jon-le0234/DoomScroller/Images/DoomScroller/01.png

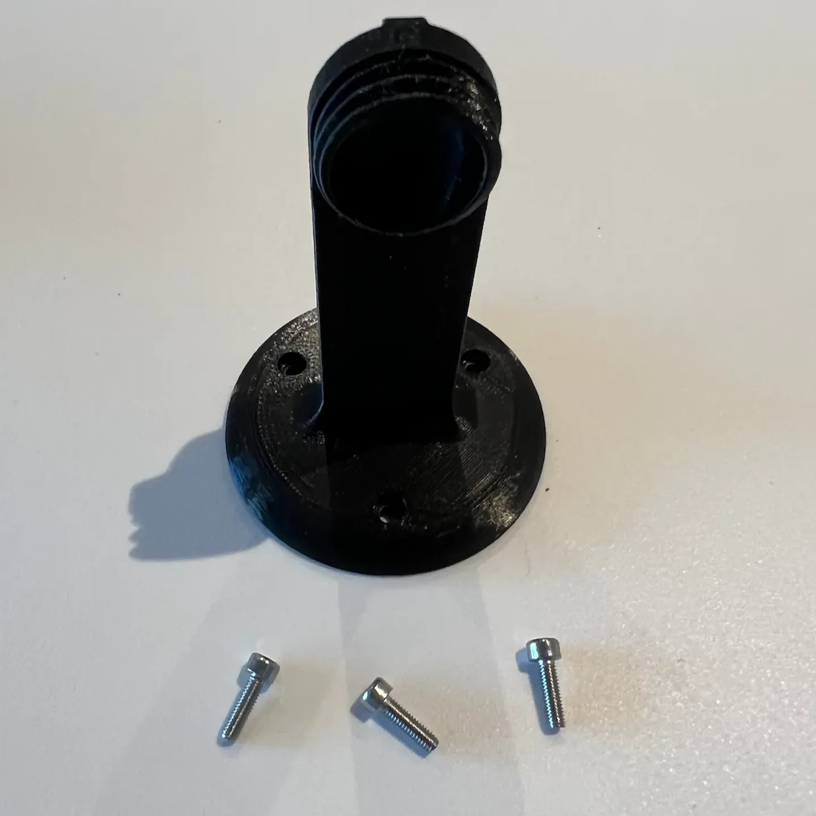
Images/DoomScroller/01.png
