jon-le0234/DoomScroller/Images/DoomScroller/02.png

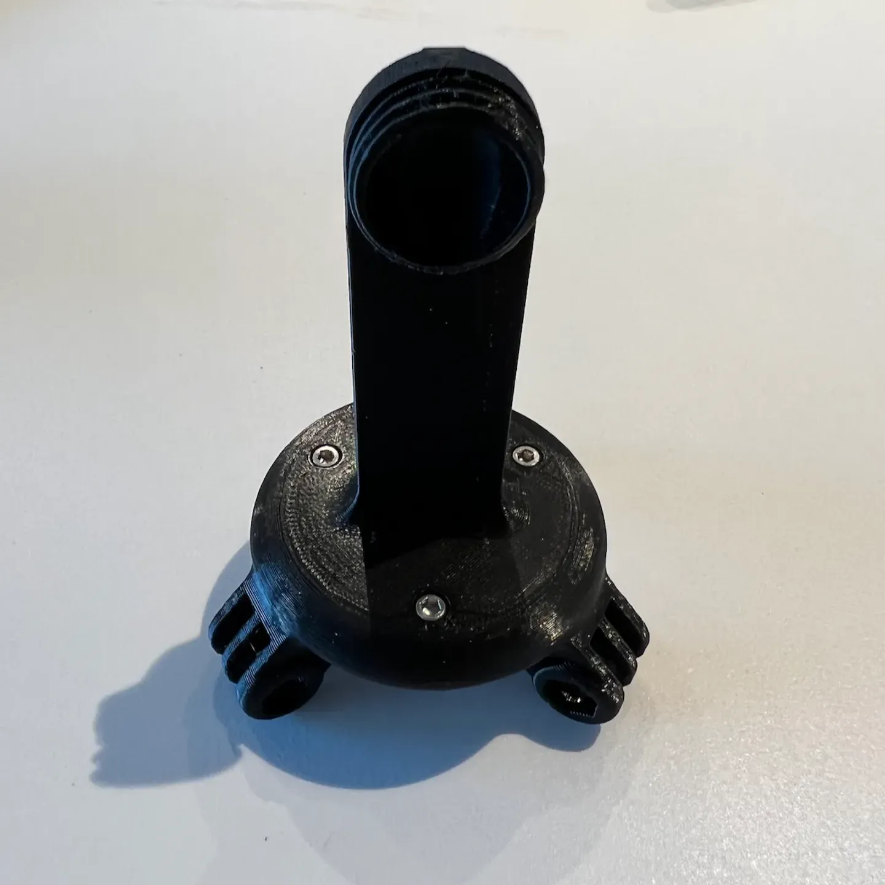
Images/DoomScroller/02.png
