jon-le0234/DoomScroller/Images/DoomScroller/03.png

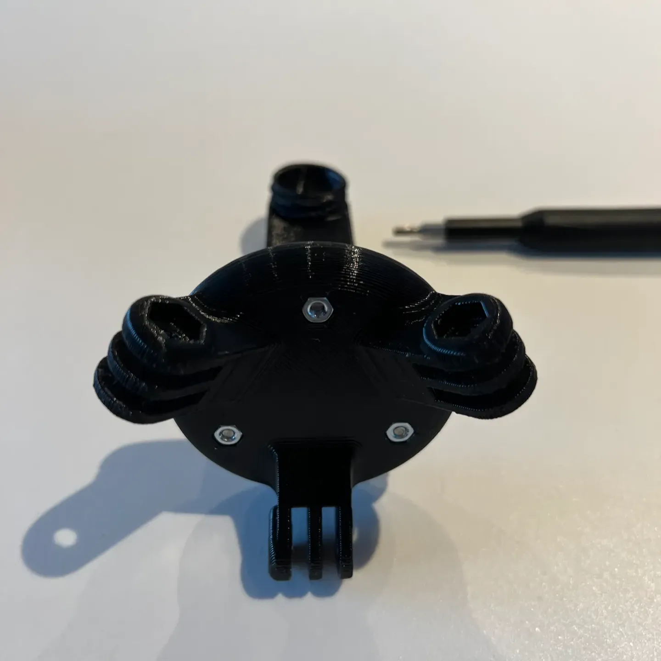
Images/DoomScroller/03.png
