jon-le0234/DoomScroller/Images/DoomScroller/04.png

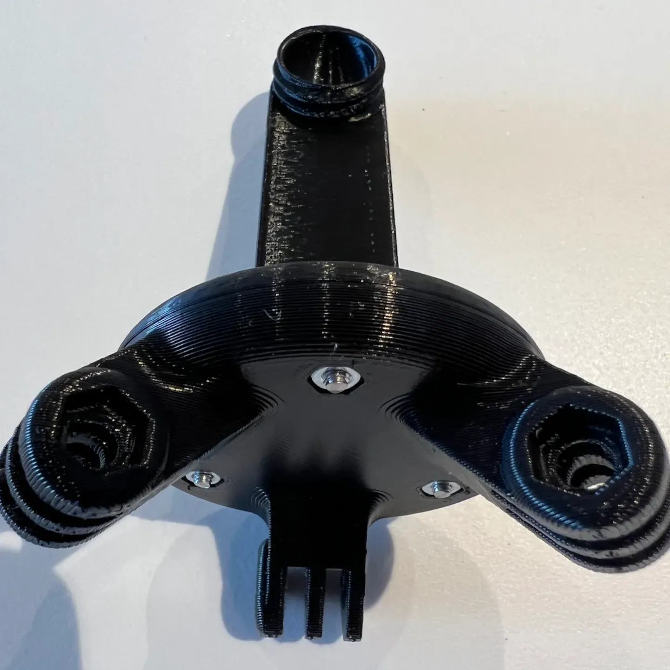
Images/DoomScroller/04.png
