jon-le0234/DoomScroller/Images/DoomScroller/05.png

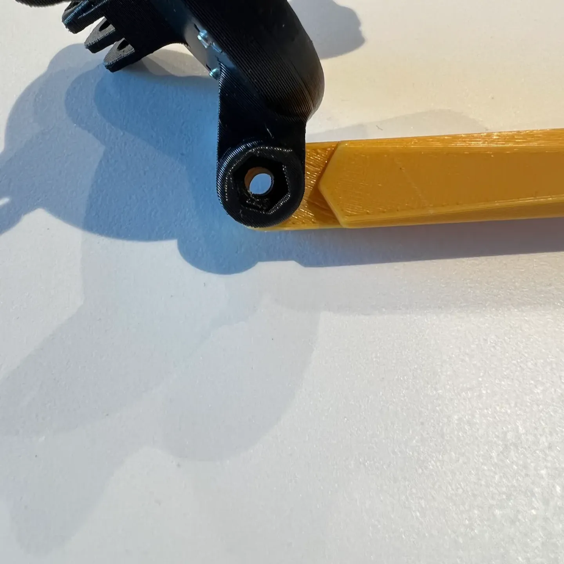
Images/DoomScroller/05.png
