jon-le0234/DoomScroller/Images/DoomScroller/06.png

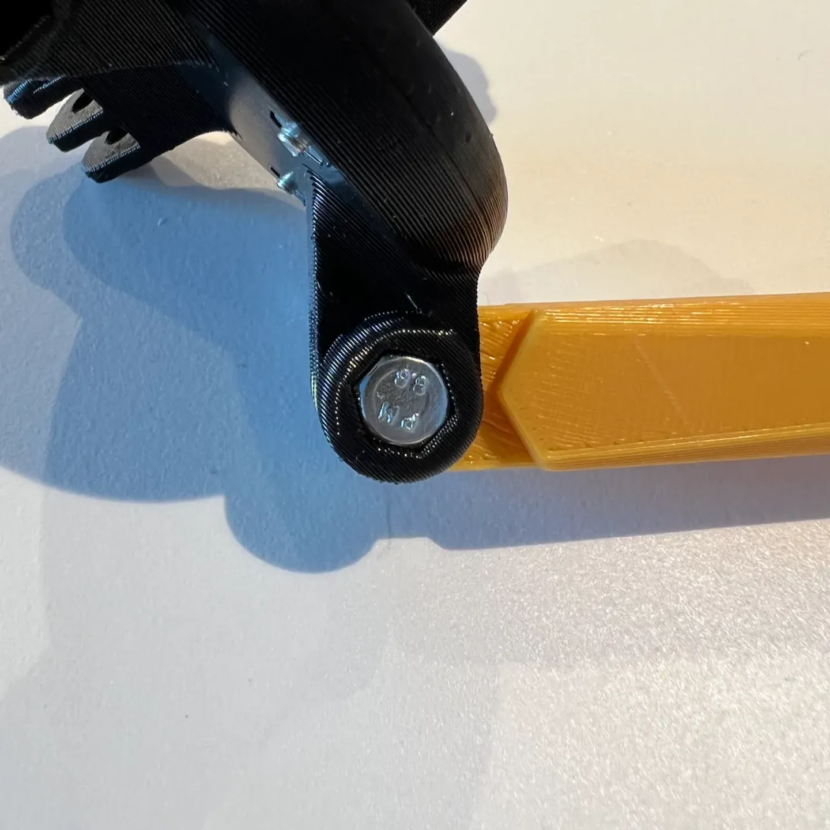
Images/DoomScroller/06.png
