jon-le0234/DoomScroller/Images/DoomScroller/07.png

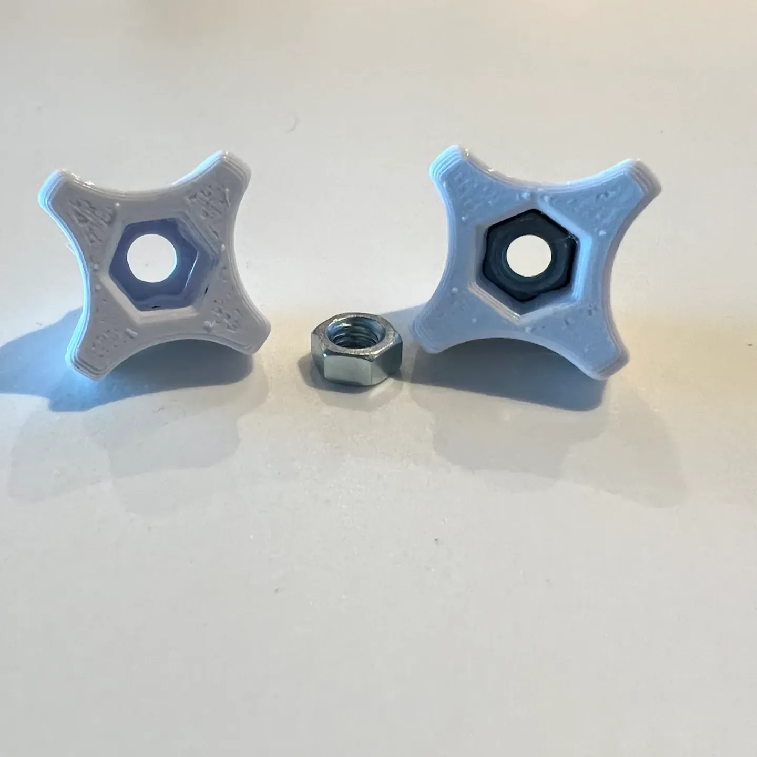
Images/DoomScroller/07.png
