jon-le0234/DoomScroller/Images/DoomScroller/08.png

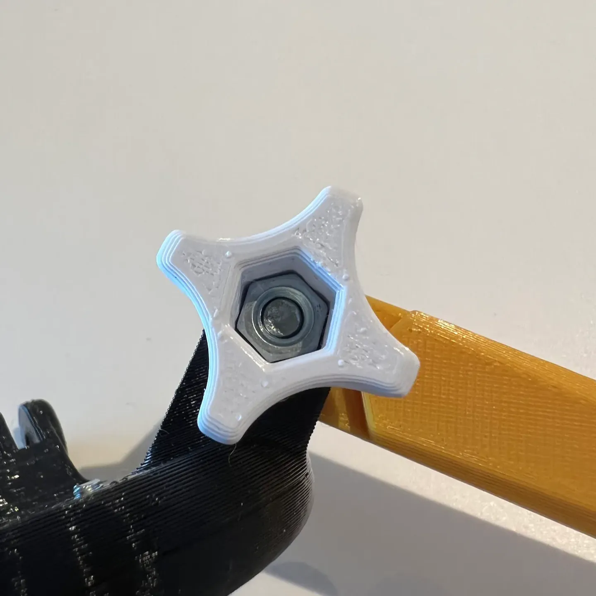
Images/DoomScroller/08.png
