jon-le0234/DoomScroller/Images/DoomScroller/09.png

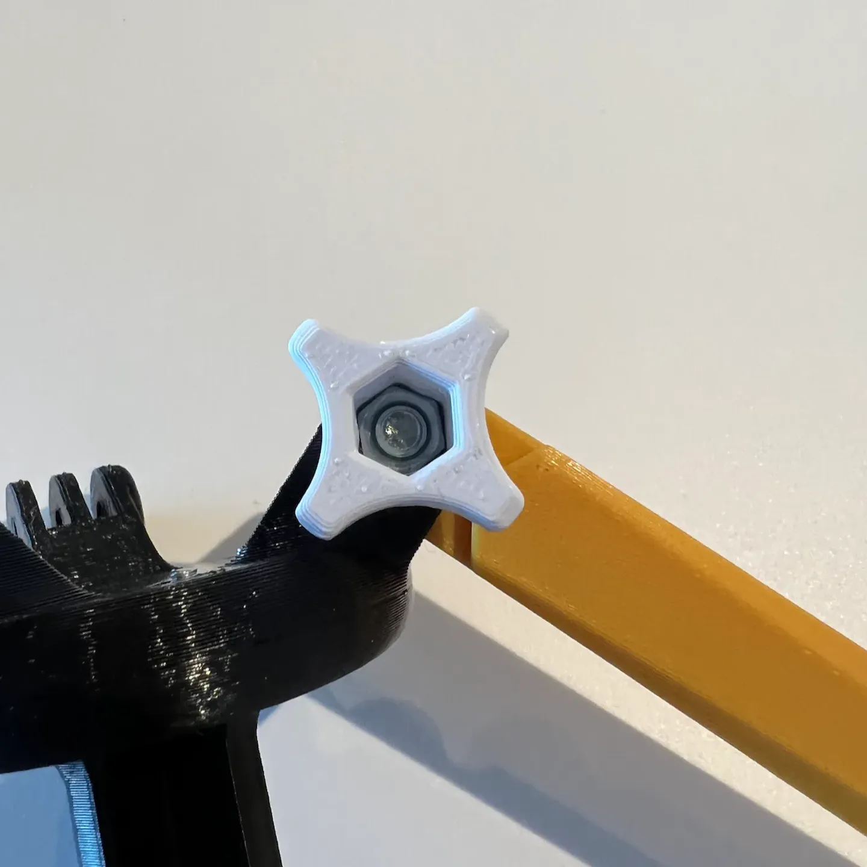
Images/DoomScroller/09.png
