jon-le0234/DoomScroller/Images/DoomScroller/10.png

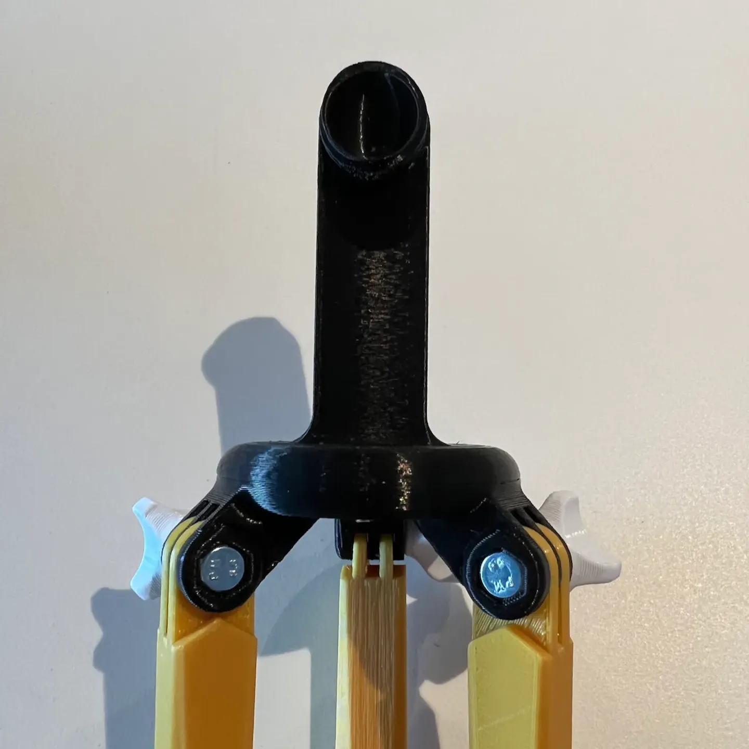
Images/DoomScroller/10.png
