jon-le0234/DoomScroller/Images/DoomScroller/11.png

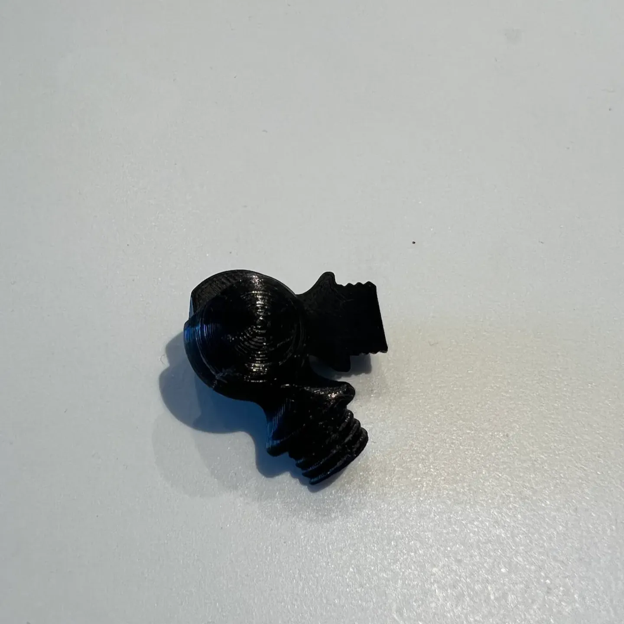
Images/DoomScroller/11.png
