jon-le0234/DoomScroller/Images/DoomScroller/12.png

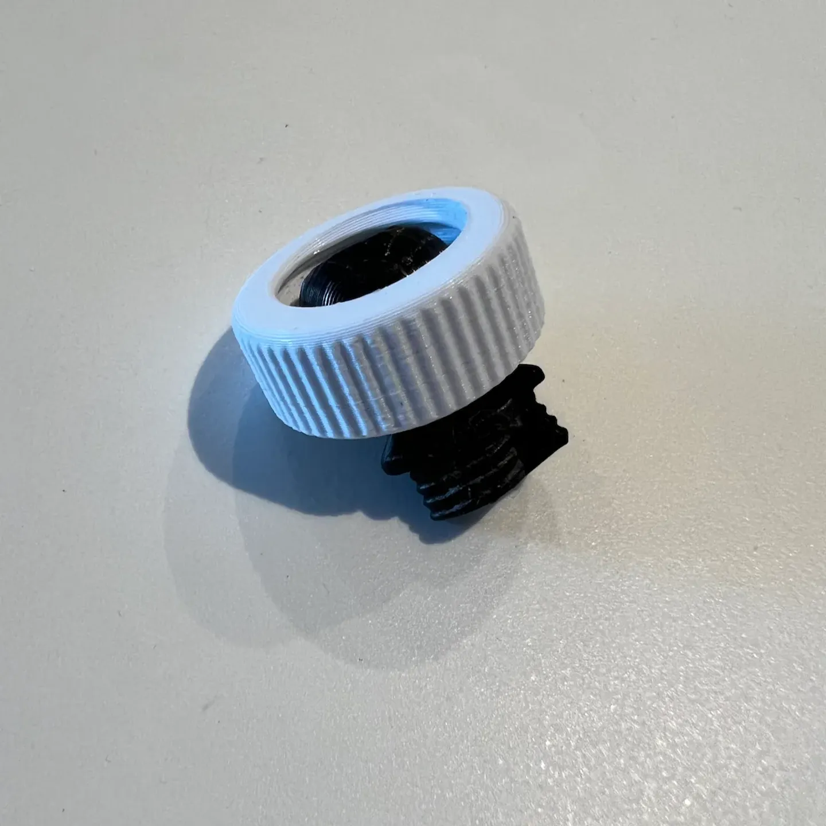
Images/DoomScroller/12.png
