jon-le0234/DoomScroller/Images/DoomScroller/13.png

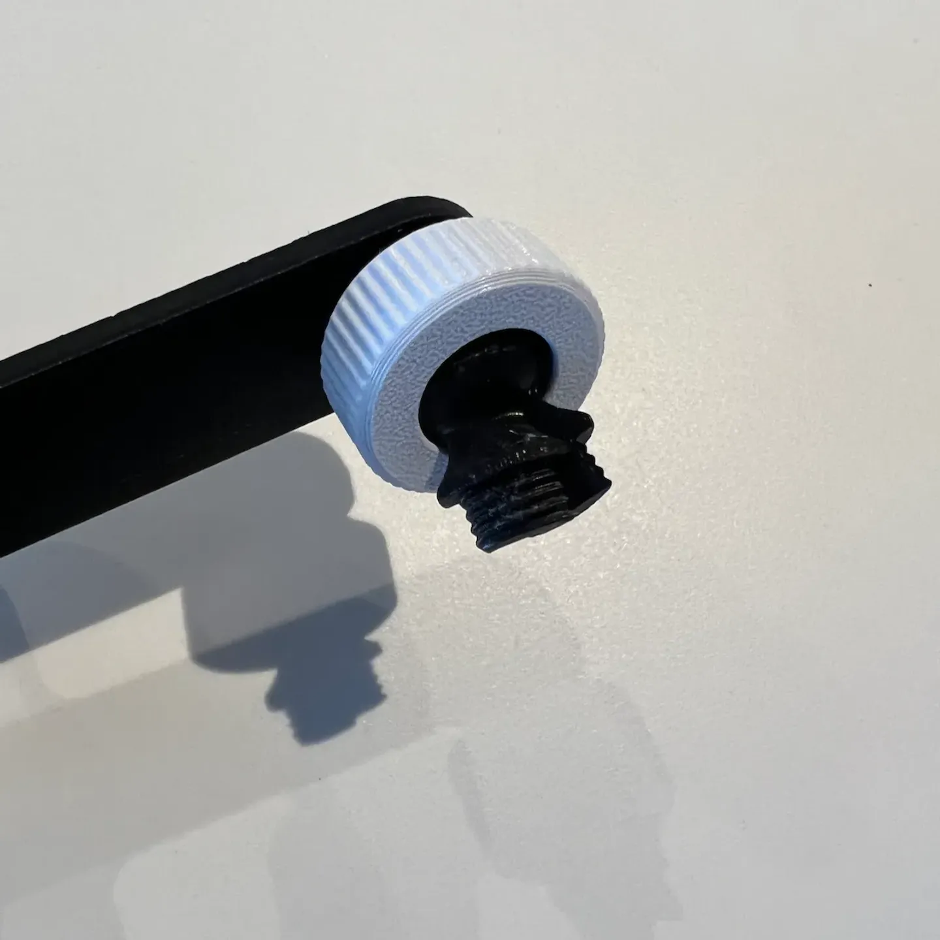
Images/DoomScroller/13.png
