jon-le0234/DoomScroller/Images/DoomScroller/14.png

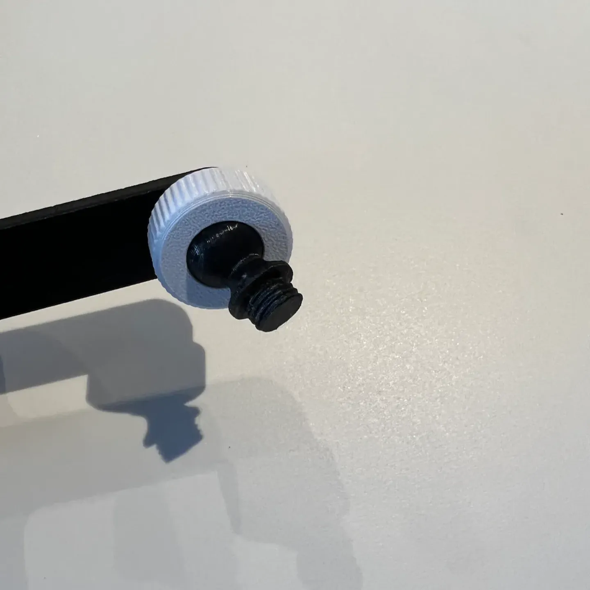
Images/DoomScroller/14.png
