jon-le0234/DoomScroller/Images/DoomScroller/15a.png

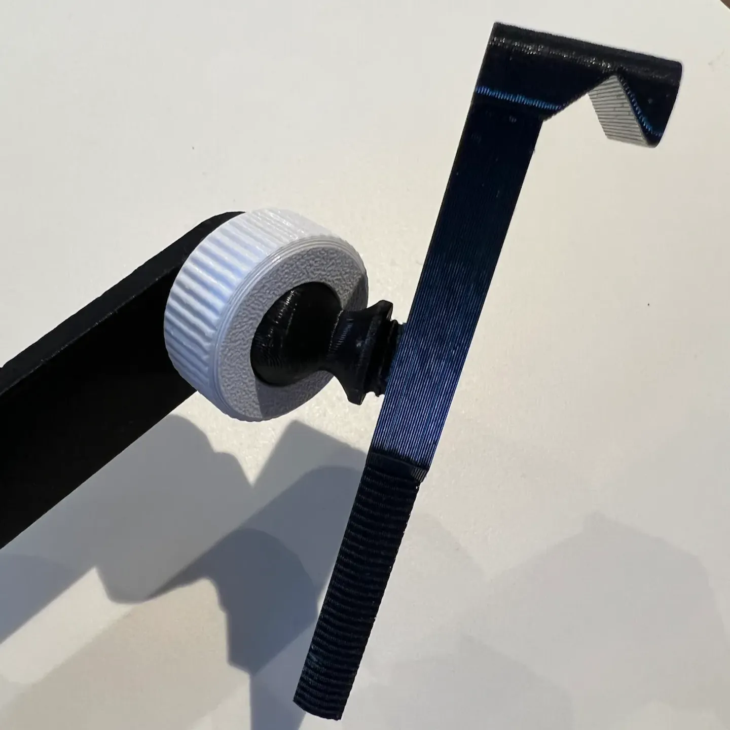
Images/DoomScroller/15a.png
