jon-le0234/DoomScroller/Images/DoomScroller/16.png

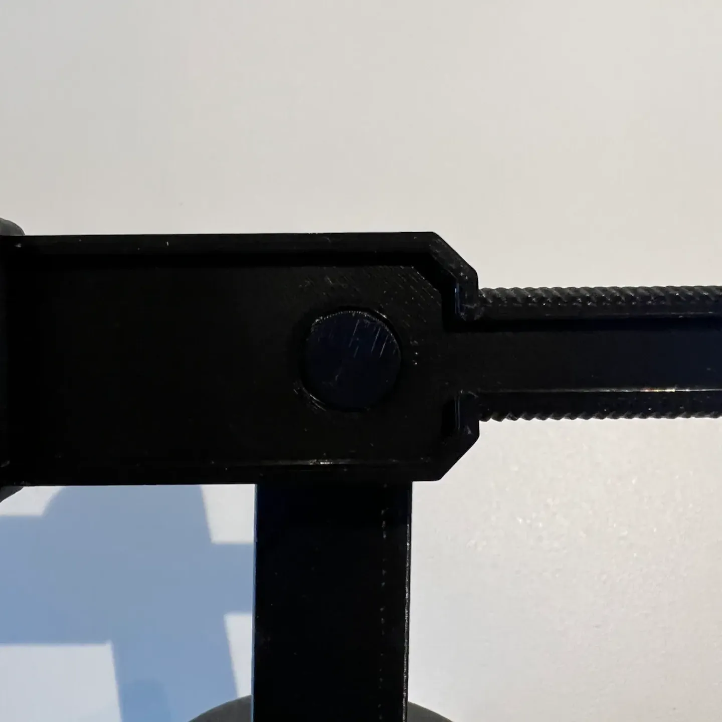
Images/DoomScroller/16.png
