jon-le0234/DoomScroller/Images/DoomScroller/17.png

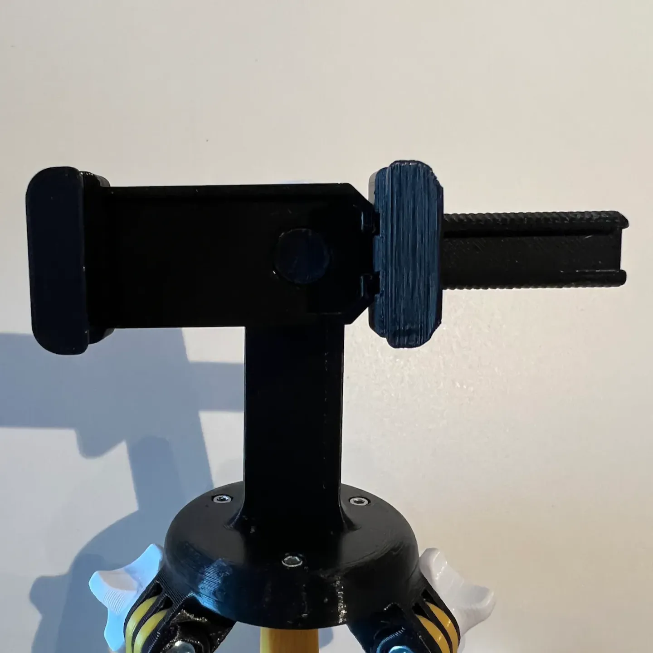
Images/DoomScroller/17.png
