jon-le0234/DoomScroller/Images/DoomScroller/18.png

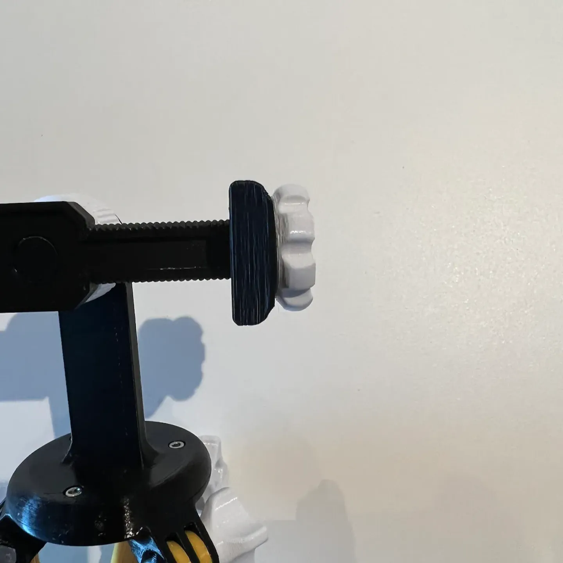
Images/DoomScroller/18.png
