jon-le0234/DoomScroller/Images/DoomScroller/black-blue-purple.png

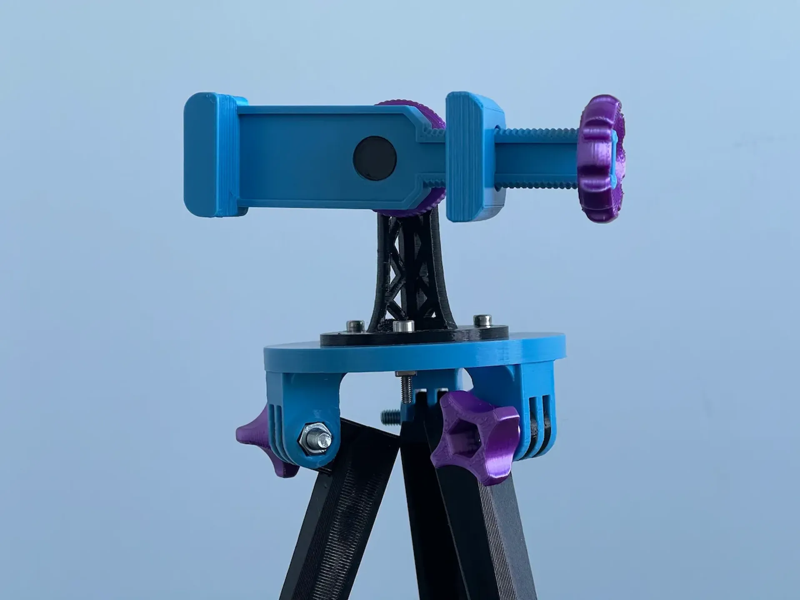
Images/DoomScroller/black-blue-purple.png
