jon-le0234/DoomScroller/Images/DoomScroller/black-blue.png

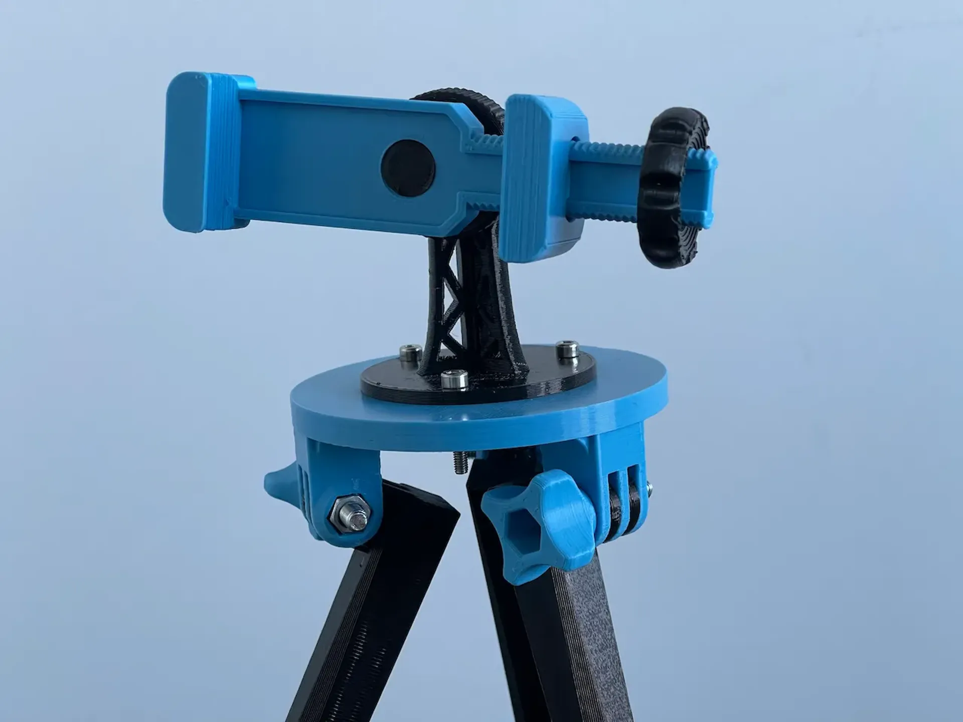
Images/DoomScroller/black-blue.png
