jon-le0234/DoomScroller/Images/DoomScroller/black-gold.png

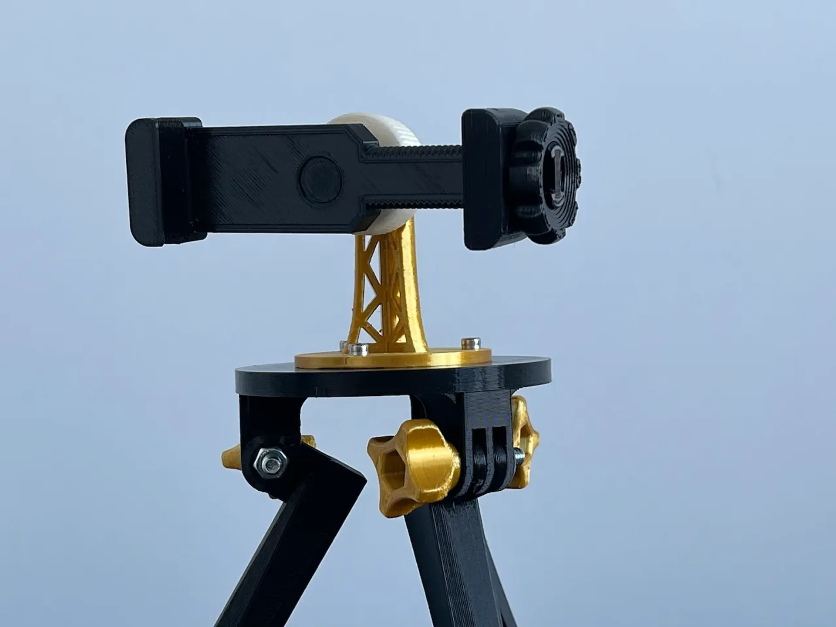
Images/DoomScroller/black-gold.png
