jon-le0234/DoomScroller/Images/DoomScroller/black-green.png

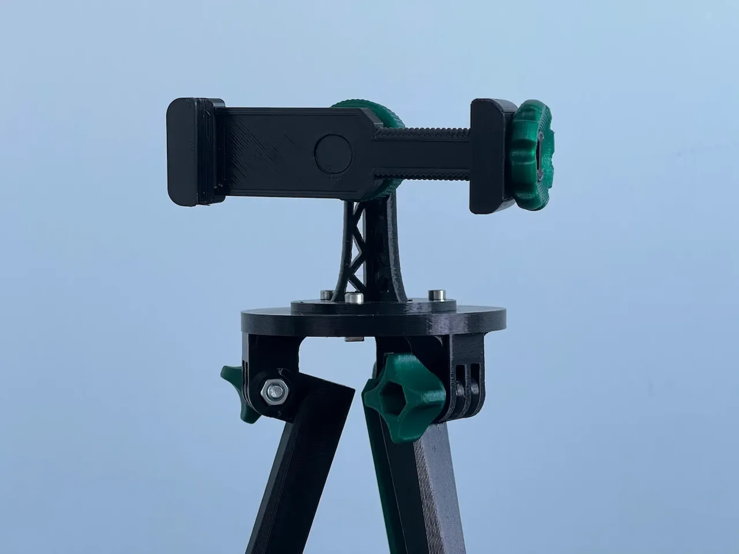
Images/DoomScroller/black-green.png
