jon-le0234/DoomScroller/Images/DoomScroller/black-purple.png

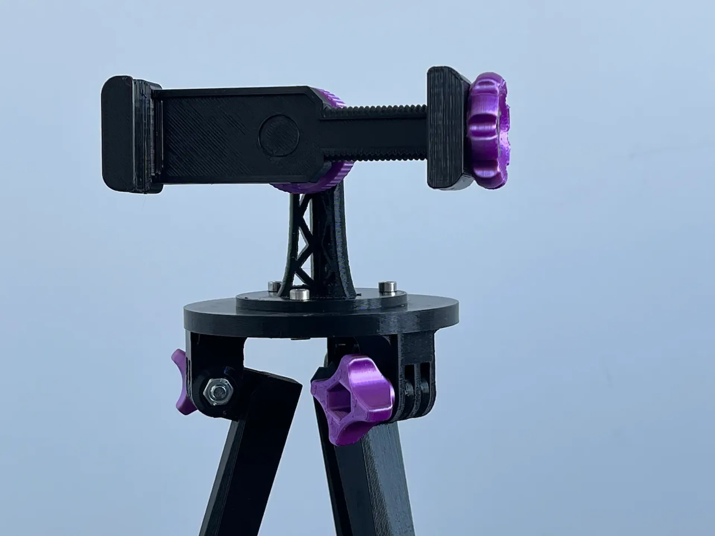
Images/DoomScroller/black-purple.png
