jon-le0234/DoomScroller/Images/DoomScroller/black-red-green.png

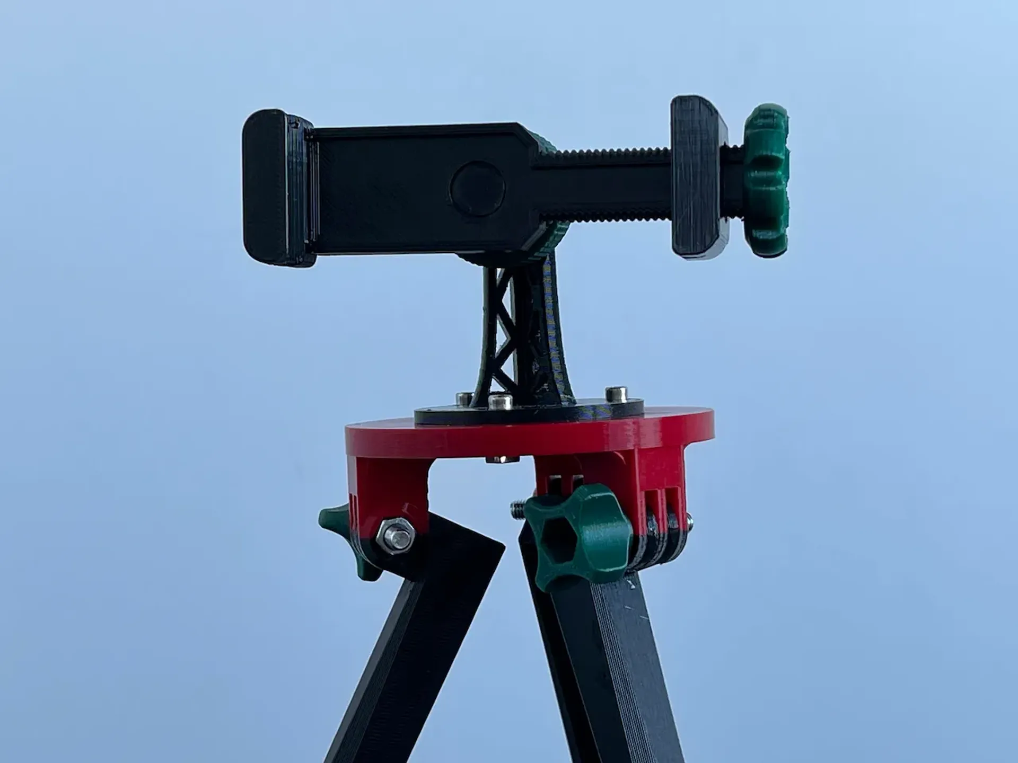
Images/DoomScroller/black-red-green.png
