jon-le0234/DoomScroller/Images/DoomScroller/black-red.png

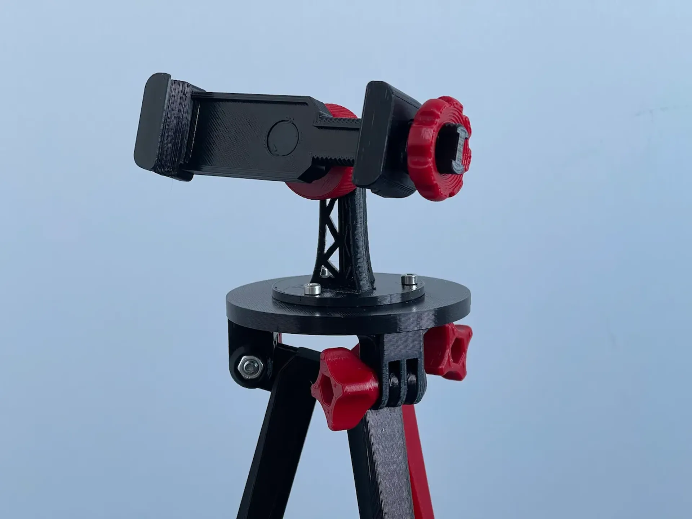
Images/DoomScroller/black-red.png
