jon-le0234/DoomScroller/Images/DoomScroller/doomscroller-panavise.png

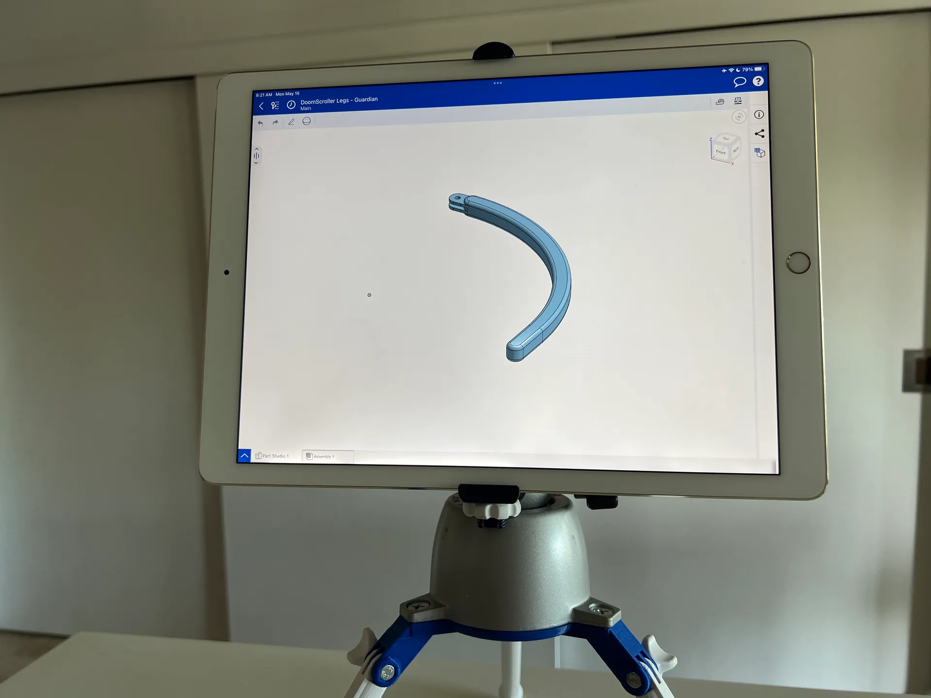
Images/DoomScroller/doomscroller-panavise.png
