jon-le0234/DoomScroller/Images/DoomScroller/gold-black.png

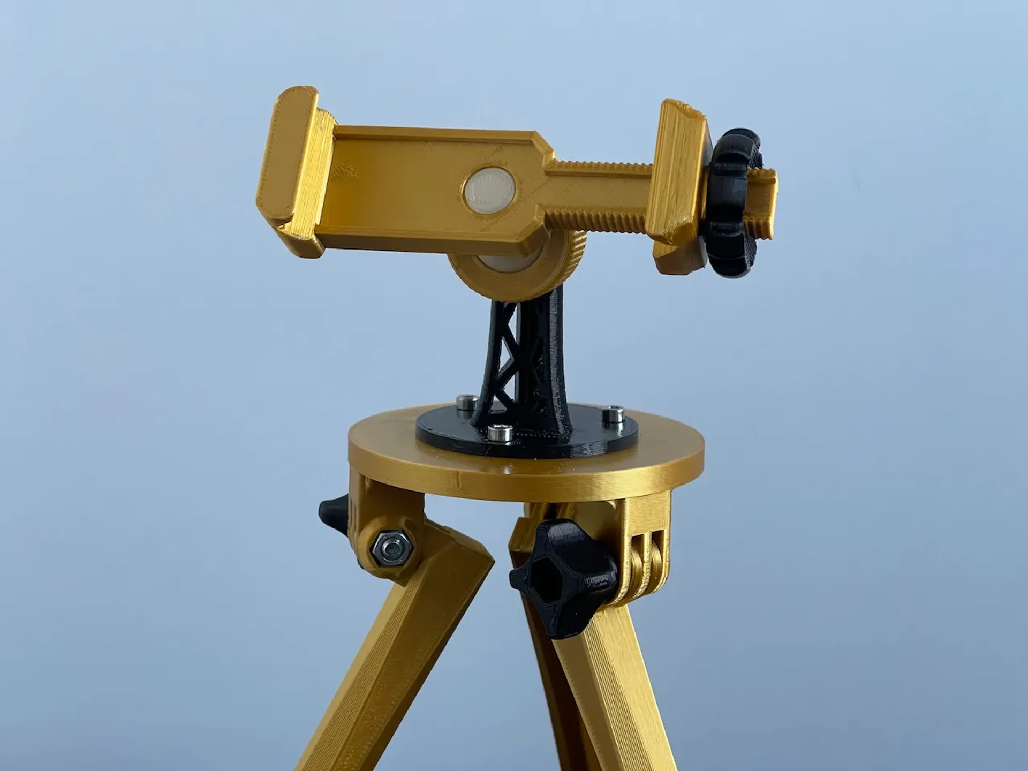
Images/DoomScroller/gold-black.png
