jon-le0234/DoomScroller/Images/DoomScroller/jon-and-jo.png

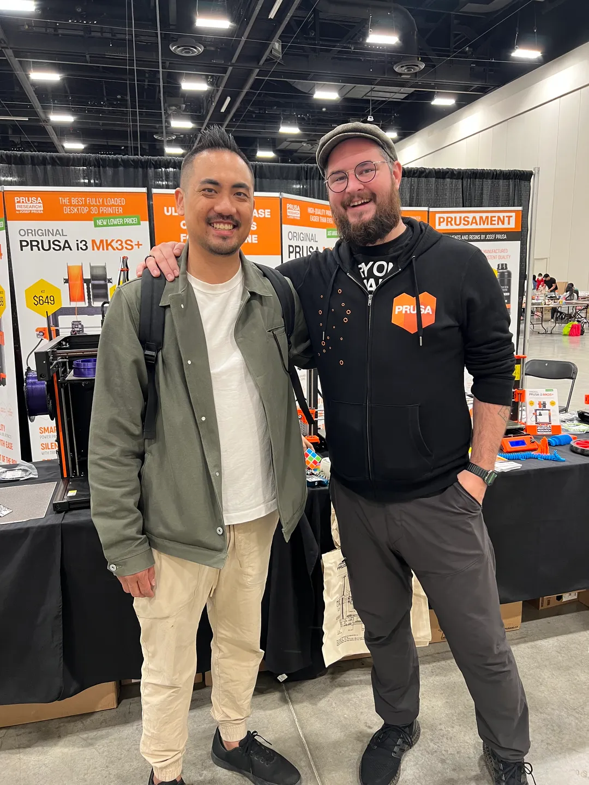
Images/DoomScroller/jon-and-jo.png
