jon-le0234/DoomScroller/Images/DoomScroller/lakers.png

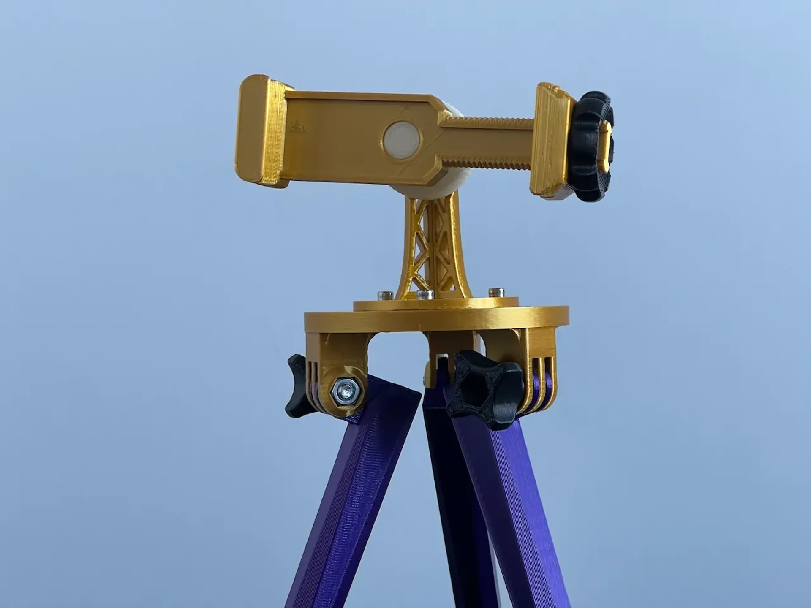
Images/DoomScroller/lakers.png
