jon-le0234/DoomScroller/Images/DoomScroller/landscape.png

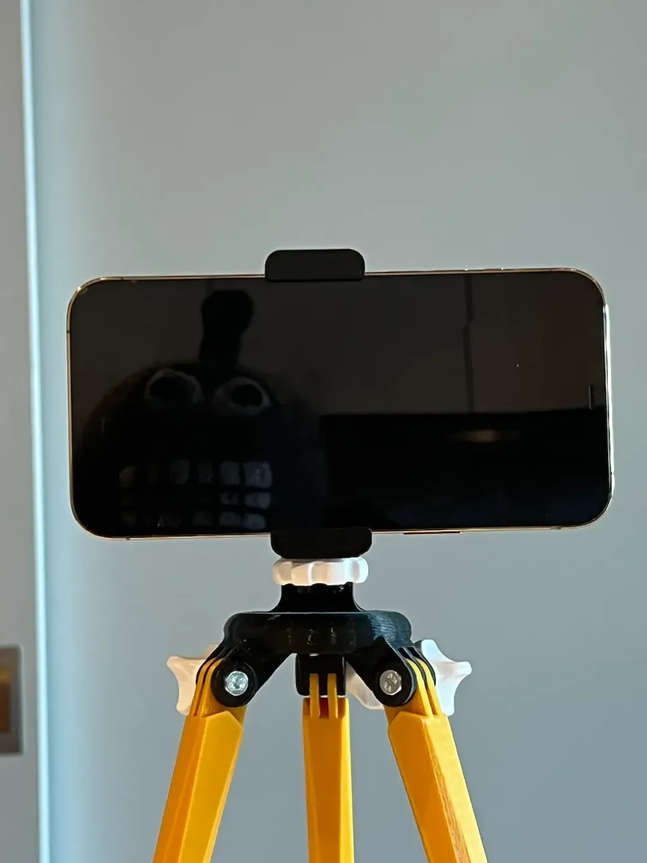
Images/DoomScroller/landscape.png
