jon-le0234/DoomScroller/Images/DoomScroller/oilers.png

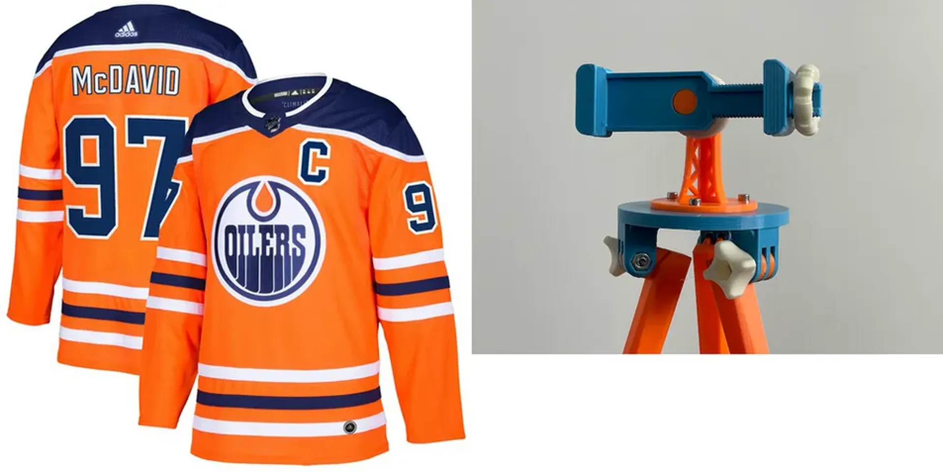
Images/DoomScroller/oilers.png
