jon-le0234/DoomScroller/Images/DoomScroller/red-purple.png

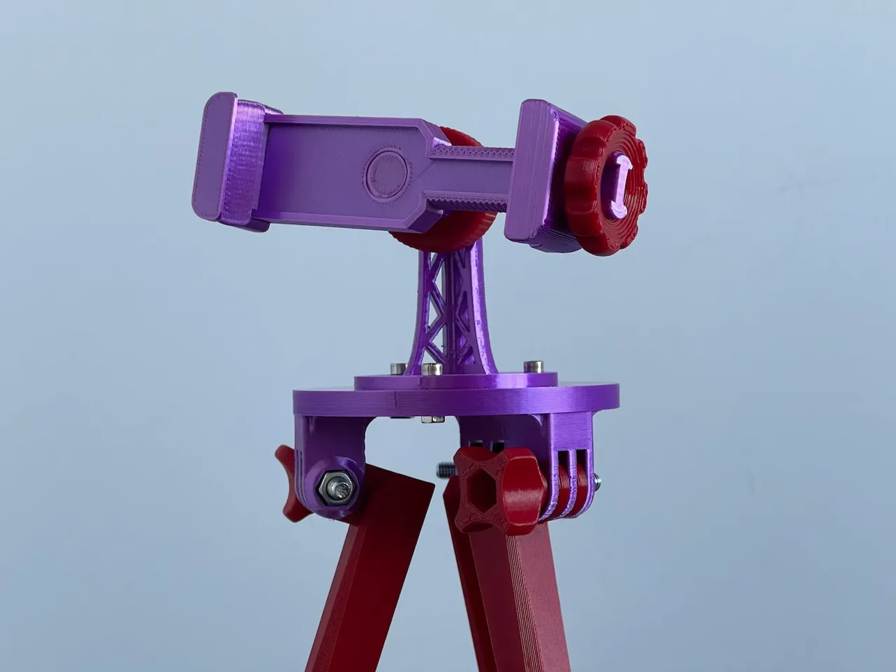
Images/DoomScroller/red-purple.png
