jon-le0234/DoomScroller/Images/Mini DoomScroller/01.png

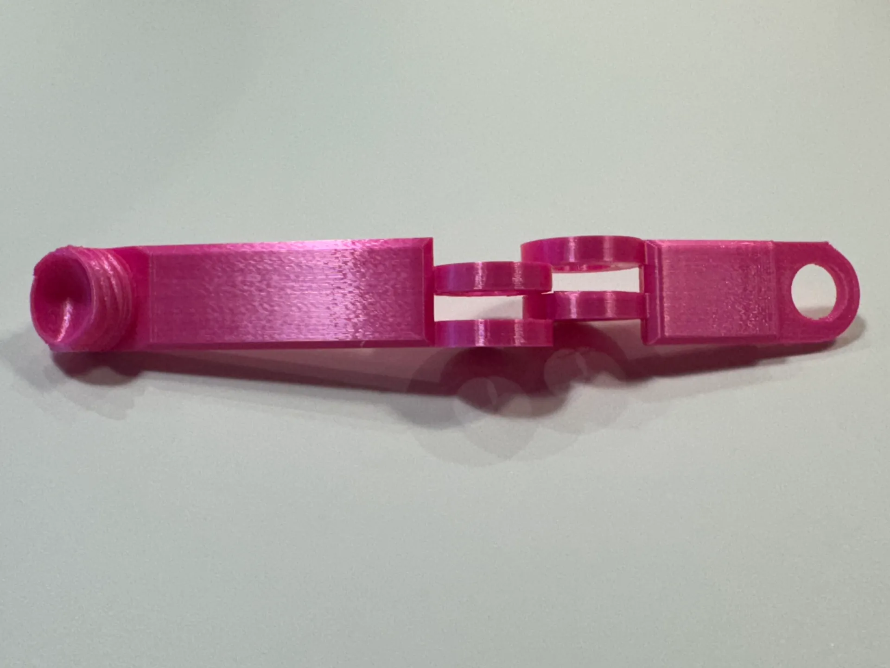
Images/Mini DoomScroller/01.png
