jon-le0234/DoomScroller/Images/Mini DoomScroller/02.png

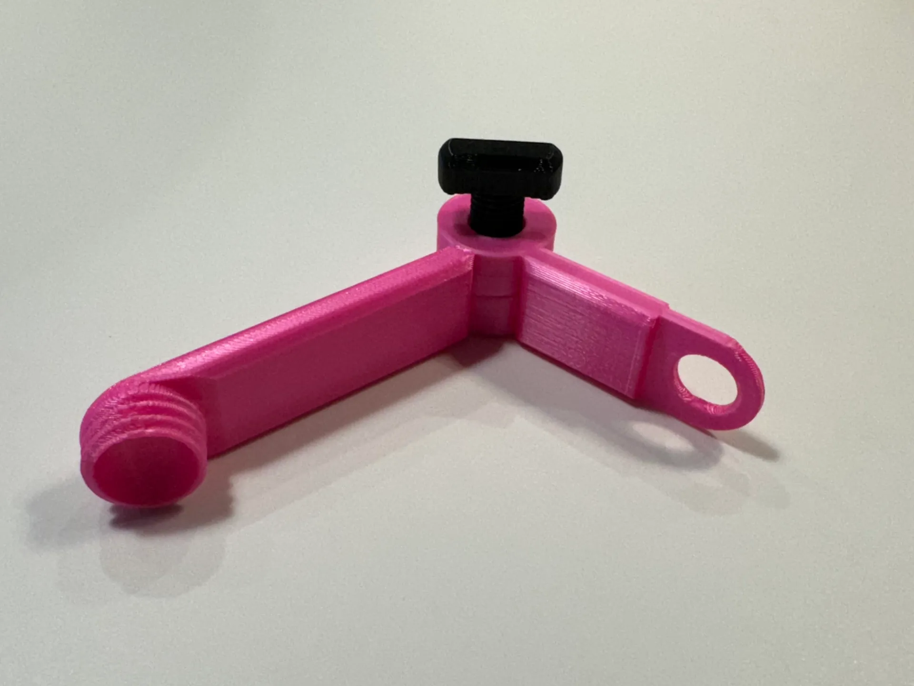
Images/Mini DoomScroller/02.png
