jon-le0234/DoomScroller/Images/Mini DoomScroller/03.png

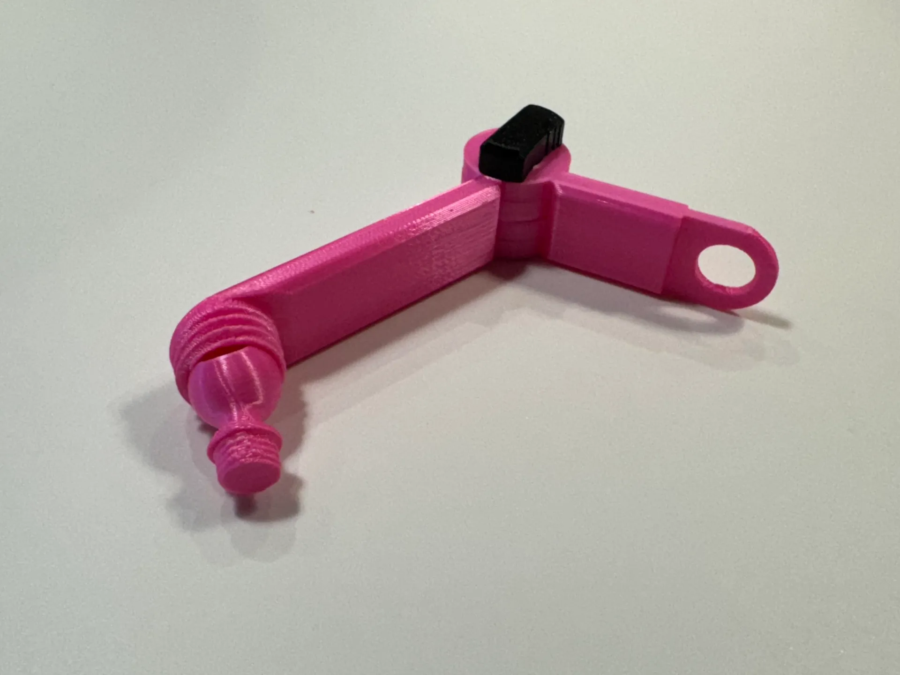
Images/Mini DoomScroller/03.png
