jon-le0234/DoomScroller/Images/Mini DoomScroller/04.png

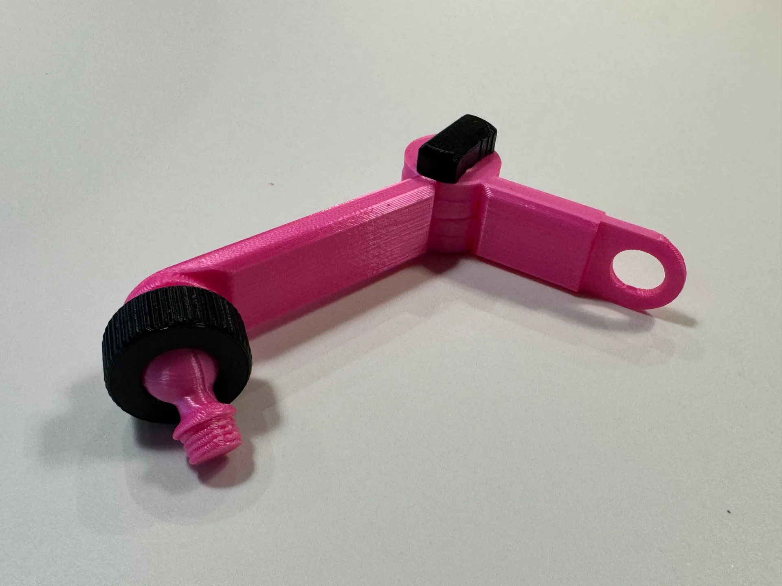
Images/Mini DoomScroller/04.png
