jon-le0234/DoomScroller/Images/Mini DoomScroller/05.png

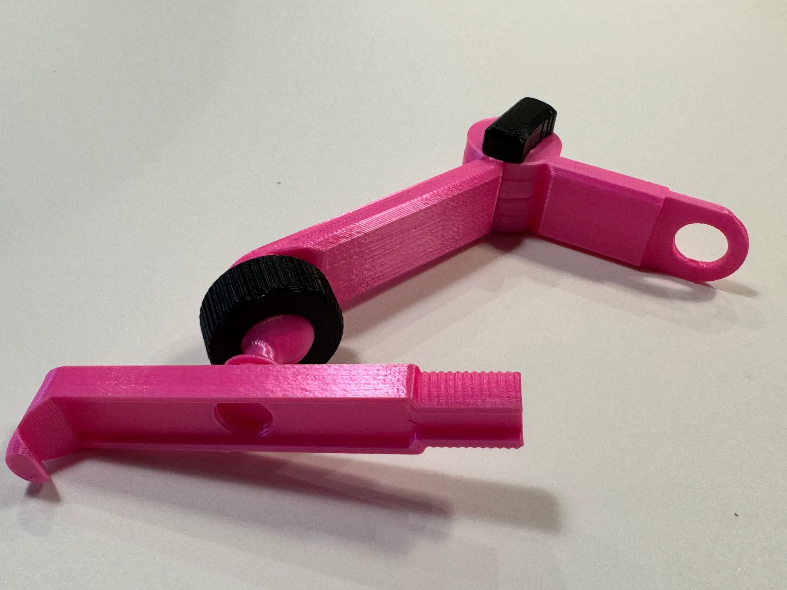
Images/Mini DoomScroller/05.png
