jon-le0234/DoomScroller/Images/Mini DoomScroller/06.png

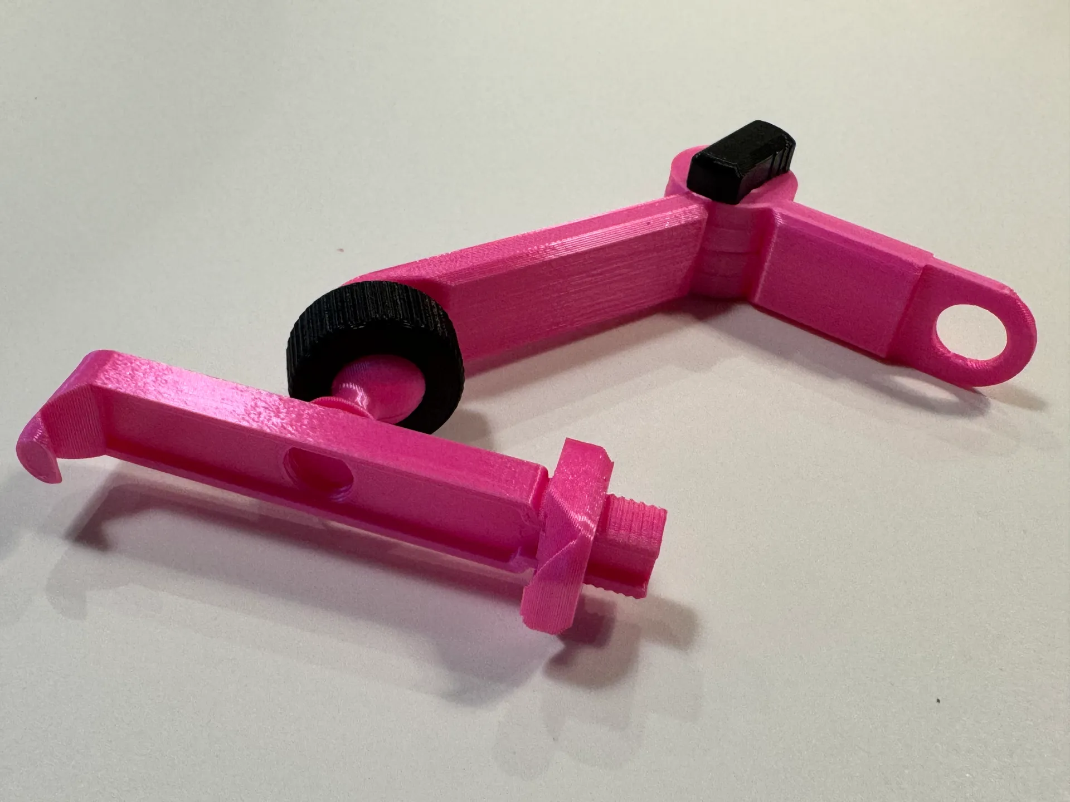
Images/Mini DoomScroller/06.png
