jon-le0234/DoomScroller/Images/Mini DoomScroller/07.png

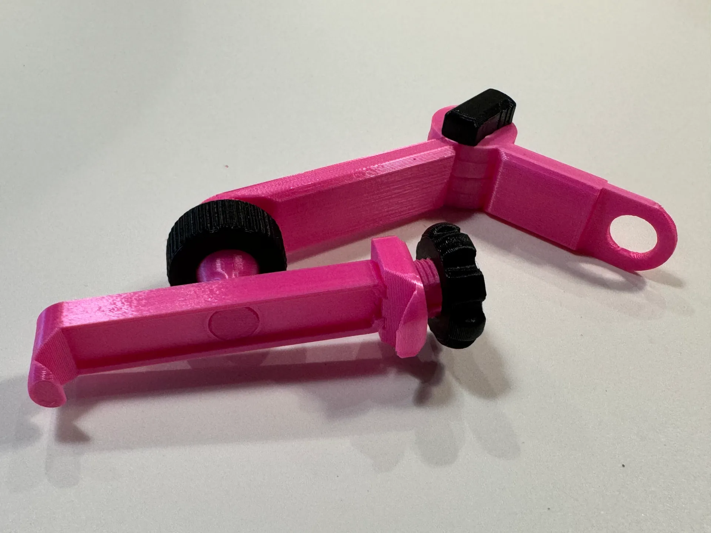
Images/Mini DoomScroller/07.png
