jon-le0234/DoomScroller/Images/Mini DoomScroller/08.png

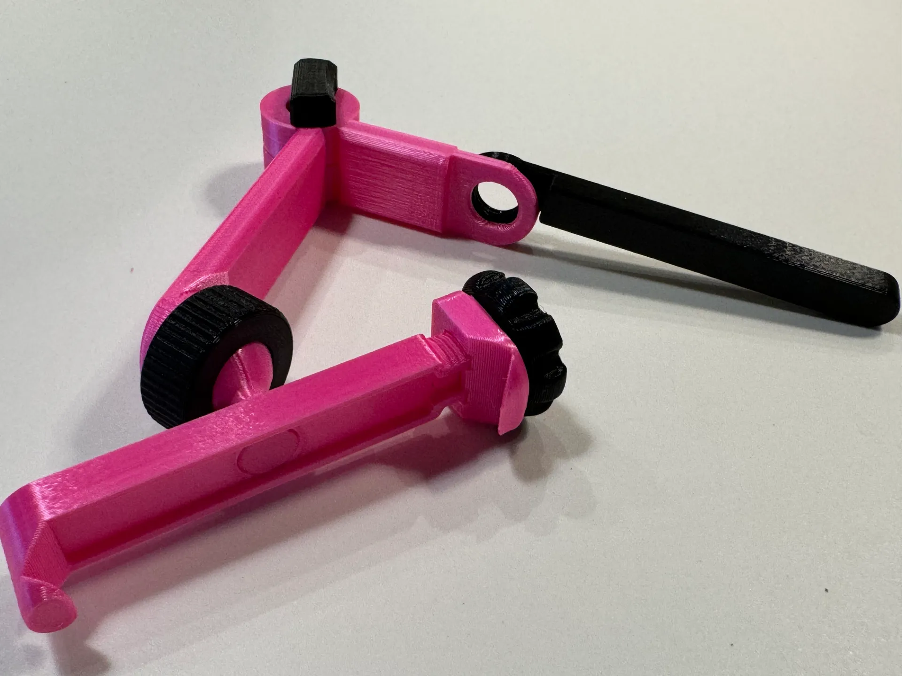
Images/Mini DoomScroller/08.png
