jon-le0234/DoomScroller/Images/Mini DoomScroller/09.png

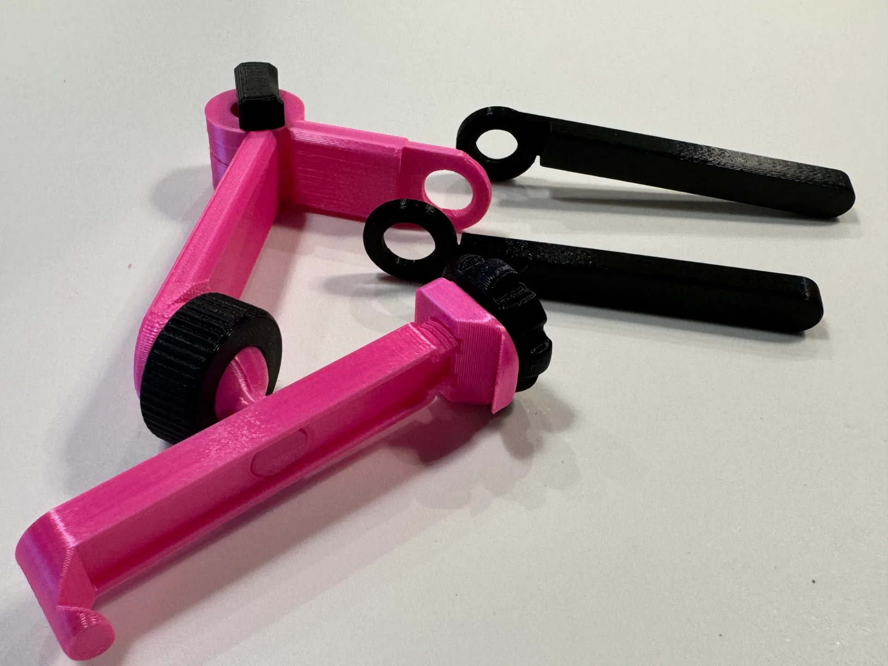
Images/Mini DoomScroller/09.png
