jon-le0234/DoomScroller/Images/Mini DoomScroller/10.png

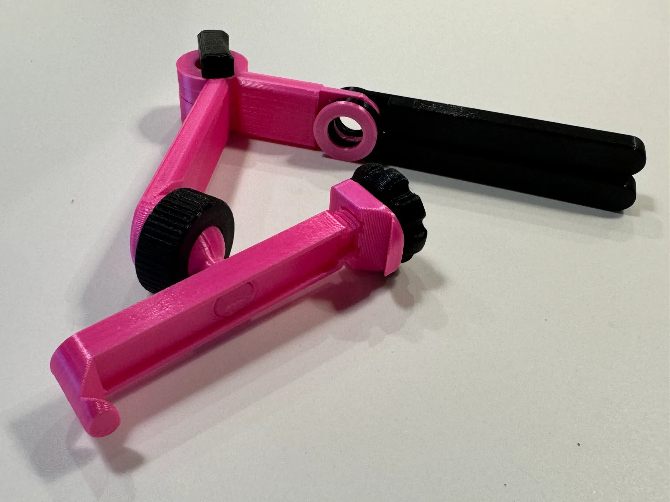
Images/Mini DoomScroller/10.png
