jon-le0234/DoomScroller/Images/Mini DoomScroller/11.png

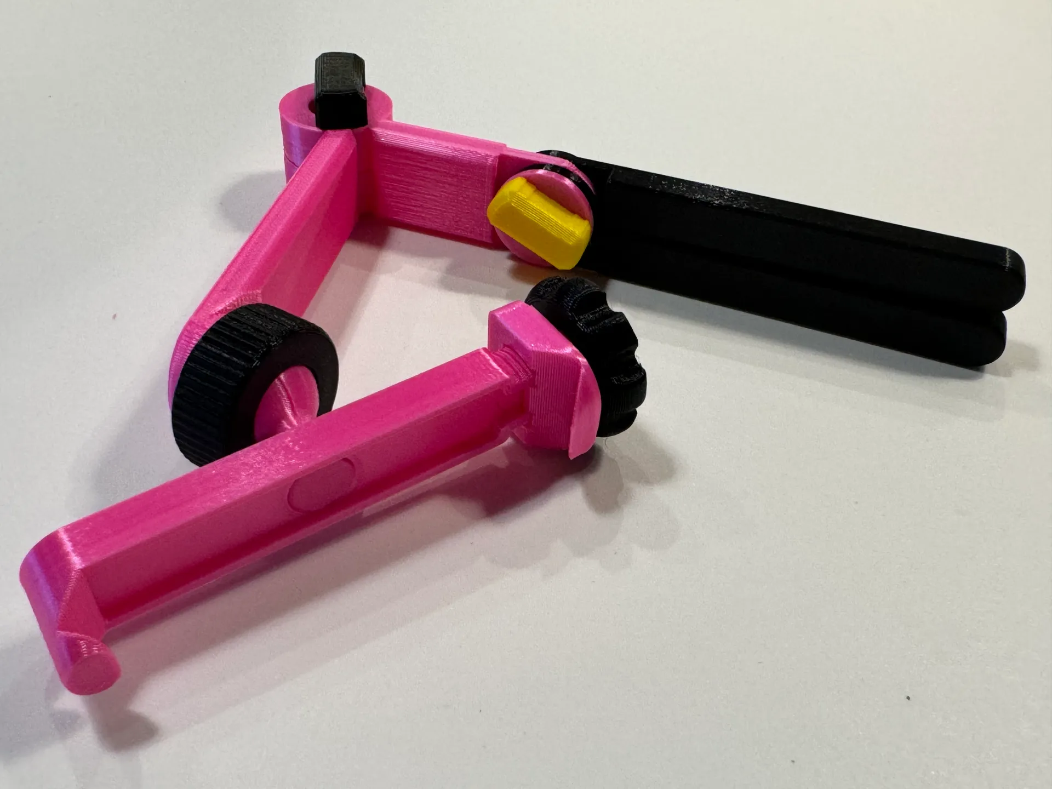
Images/Mini DoomScroller/11.png
