jon-le0234/DoomScroller/Images/Mini DoomScroller/12.png

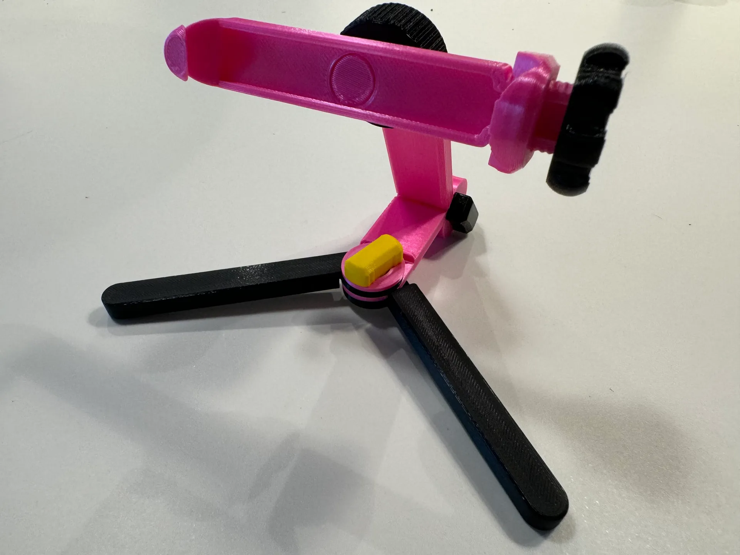
Images/Mini DoomScroller/12.png
