jon-le0234/DoomScroller/Images/Mini DoomScroller/13.png

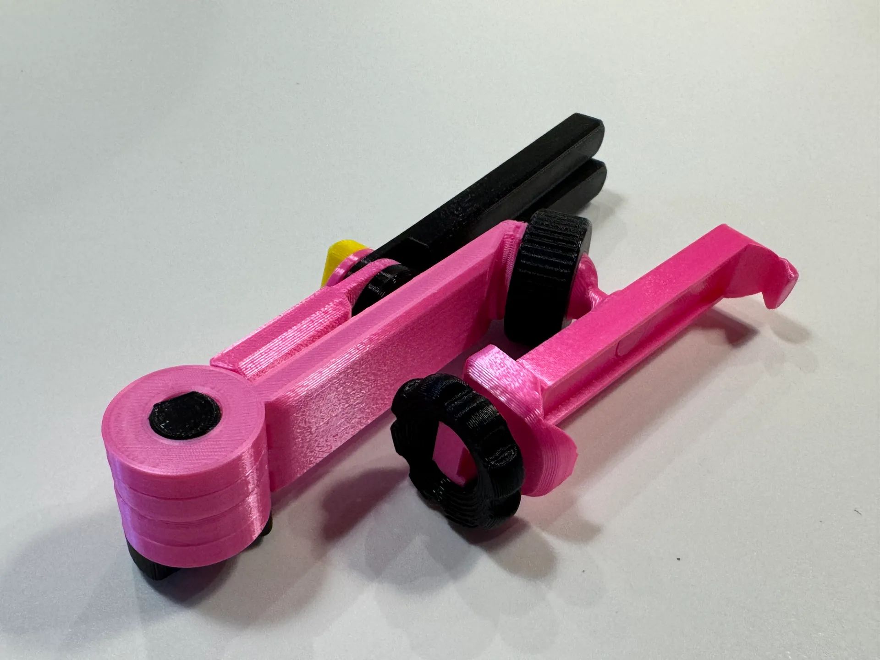
Images/Mini DoomScroller/13.png
