jon-le0234/DoomScroller/Images/Mini DoomScroller/MagFace-iOS17-StandBy.png

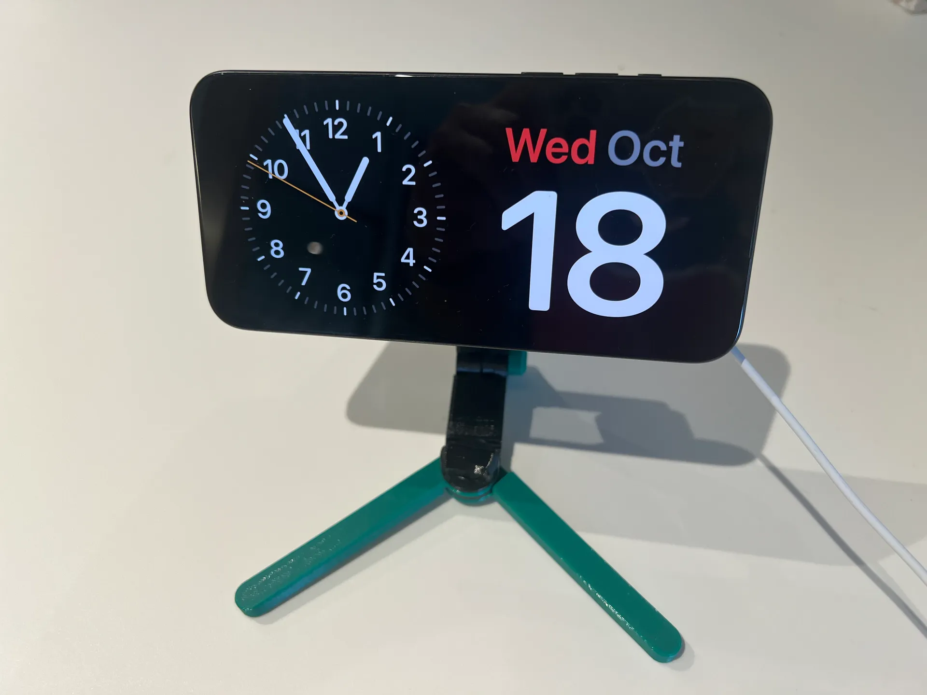
Images/Mini DoomScroller/MagFace-iOS17-StandBy.png
