jon-le0234/DoomScroller/Images/Mini DoomScroller/MK3S-PrusaSlicer-support-settings.png

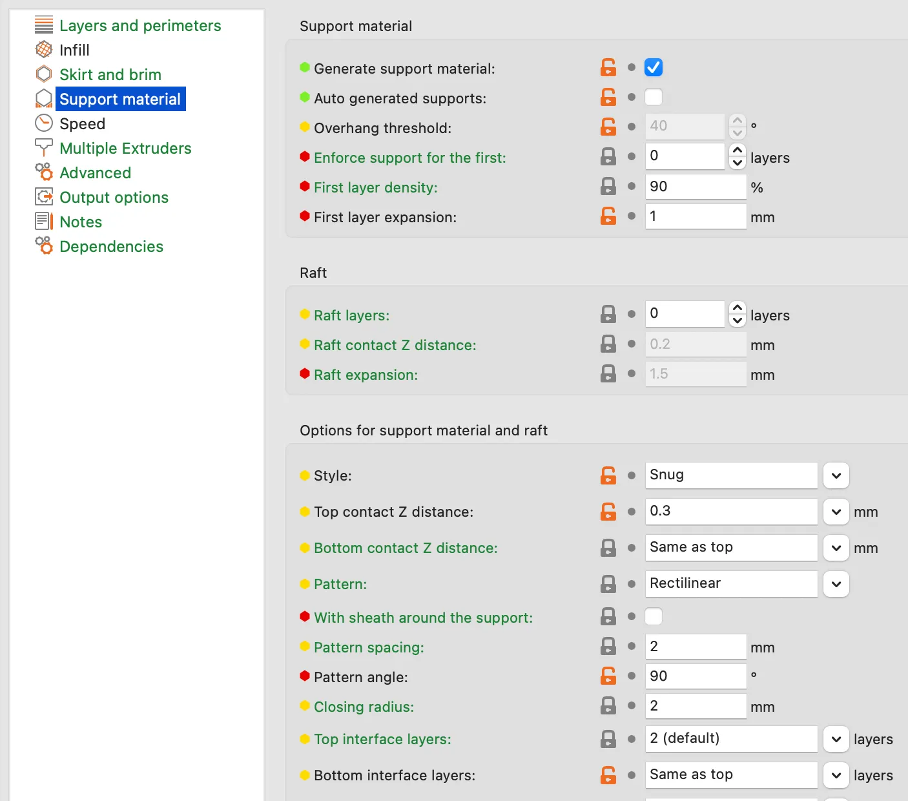
Images/Mini DoomScroller/MK3S-PrusaSlicer-support-settings.png
