jon-le0234/DoomScroller/Images/Mini DoomScroller/open-as-project.png

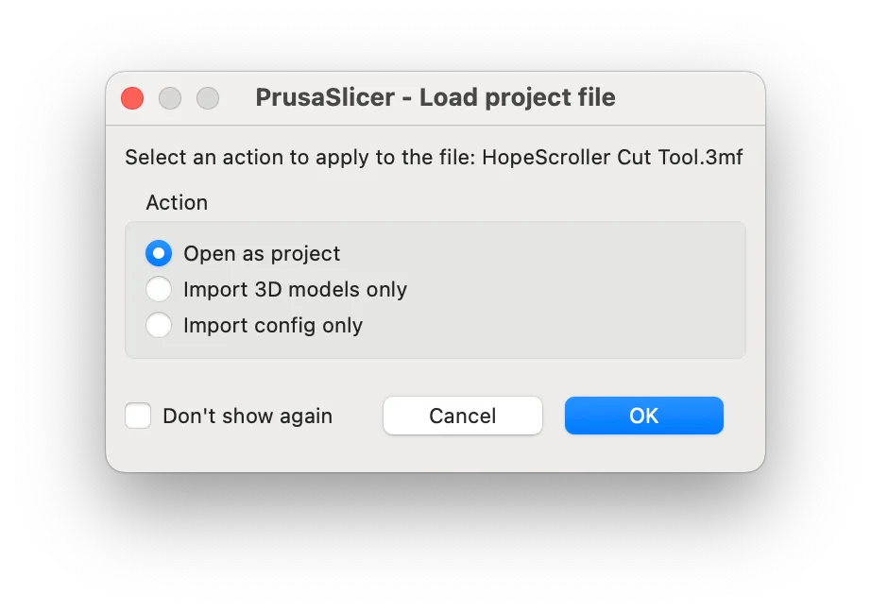
Images/Mini DoomScroller/open-as-project.png
