jon-le0234/DoomScroller/3D-Models/Mounts/Clamps/Smartphone Models/Galaxy Note 10+/DoomScroller - Clamp frame-Galaxy Note 10+.3mf

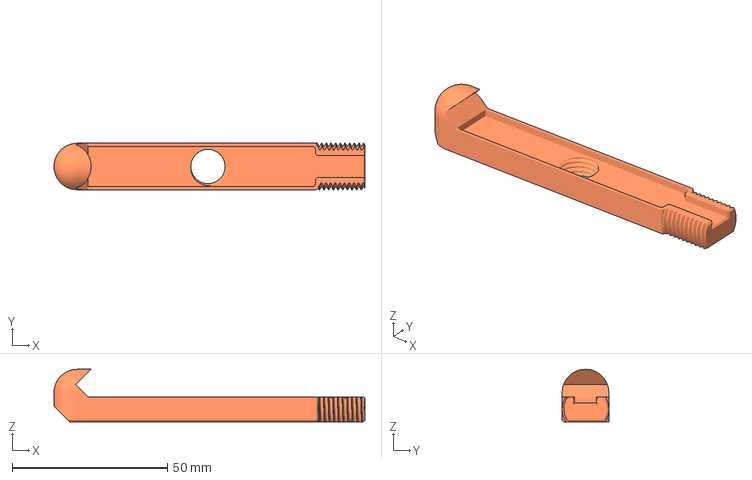
[picture p69: CAD file, 2024-01-22]
3D-Models/Mounts/Clamps/Smartphone Models/Galaxy Note 10+/DoomScroller - Clamp frame-Galaxy Note 10+.3mf
100.1 x 15.0 x 16.9 mm
