jon-le0234/DoomScroller/3D-Models/Mounts/Clamps/Smartphone Models/Galaxy Note 10/DoomScroller - Clamp movable jaw-Galaxy Note 10.3mf

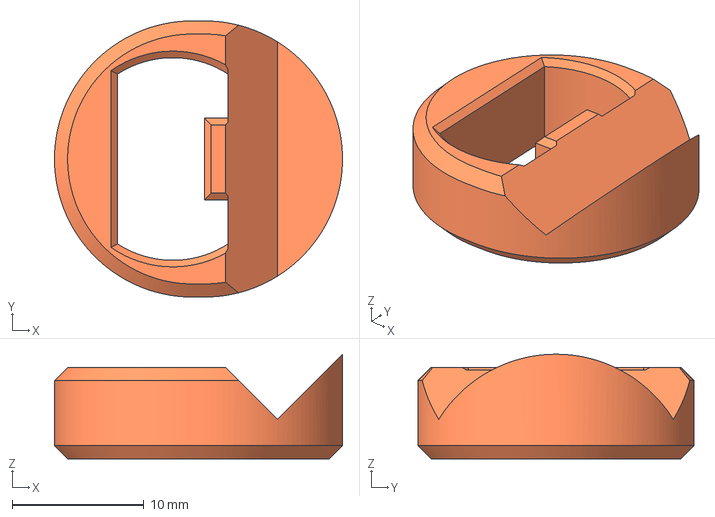
[picture p70: CAD file, 2024-01-22]
3D-Models/Mounts/Clamps/Smartphone Models/Galaxy Note 10/DoomScroller - Clamp movable jaw-Galaxy Note 10.3mf
21.9 x 21.0 x 7.95 mm
