jon-le0234/DoomScroller/3D-Models/Mounts/Clamps/Smartphone Models/Galaxy S20 Ultra 5G/DoomScroller - Clamp frame-Galaxy S20 Ultra 5G.3mf

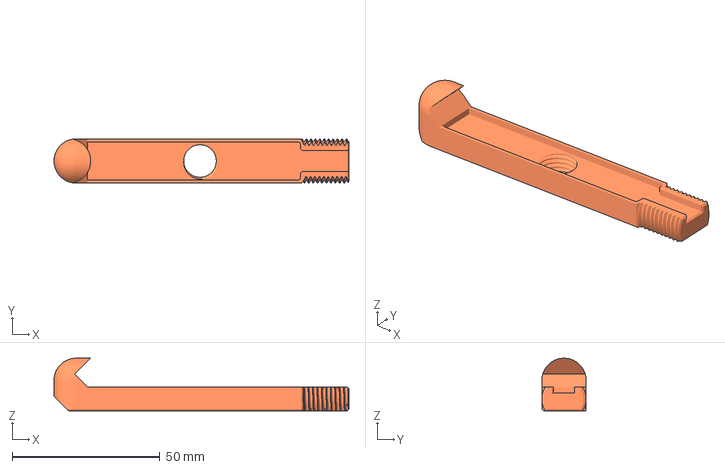
[picture p71: CAD file, 2024-01-22]
3D-Models/Mounts/Clamps/Smartphone Models/Galaxy S20 Ultra 5G/DoomScroller - Clamp frame-Galaxy S20 Ultra 5G.3mf
99.8 x 15.0 x 17.8 mm
