jon-le0234/DoomScroller/3D-Models/Mounts/Clamps/Smartphone Models/Galaxy S21 5G/DoomScroller - Clamp frame-Galaxy S21 5G.3mf

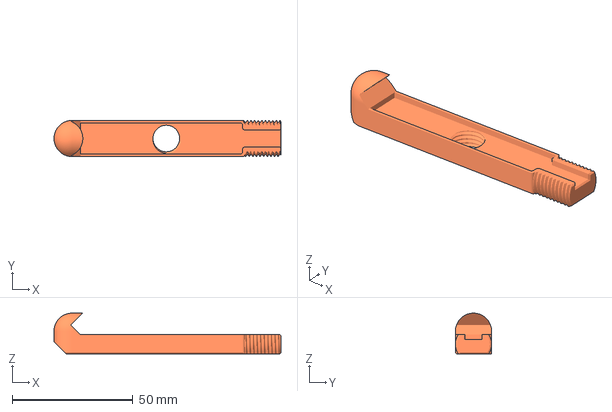
[picture p72: CAD file, 2024-01-22]
3D-Models/Mounts/Clamps/Smartphone Models/Galaxy S21 5G/DoomScroller - Clamp frame-Galaxy S21 5G.3mf
94.1 x 15.0 x 16.9 mm
