jon-le0234/DoomScroller/3D-Models/Mounts/Clamps/Smartphone Models/Galaxy S21+ 5G/DoomScroller - Clamp movable jaw-Galaxy S21+ 5G.3mf

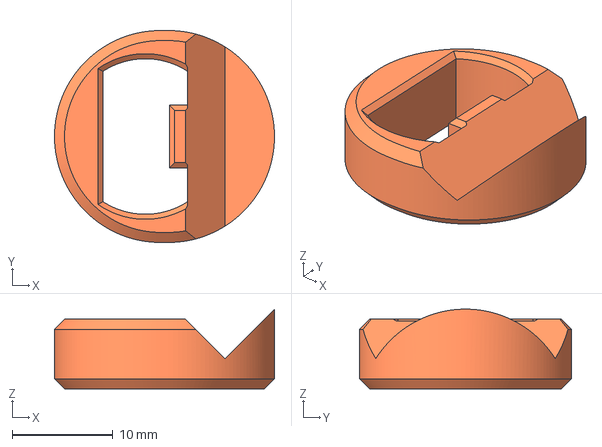
[picture p73: CAD file, 2024-01-22]
3D-Models/Mounts/Clamps/Smartphone Models/Galaxy S21+ 5G/DoomScroller - Clamp movable jaw-Galaxy S21+ 5G.3mf
21.8 x 21.0 x 7.90 mm
