jon-le0234/DoomScroller/3D-Models/Mounts/Clamps/Smartphone Models/Galaxy S22 Ultra/DoomScroller - Clamp frame-Galaxy S22 Ultra.3mf

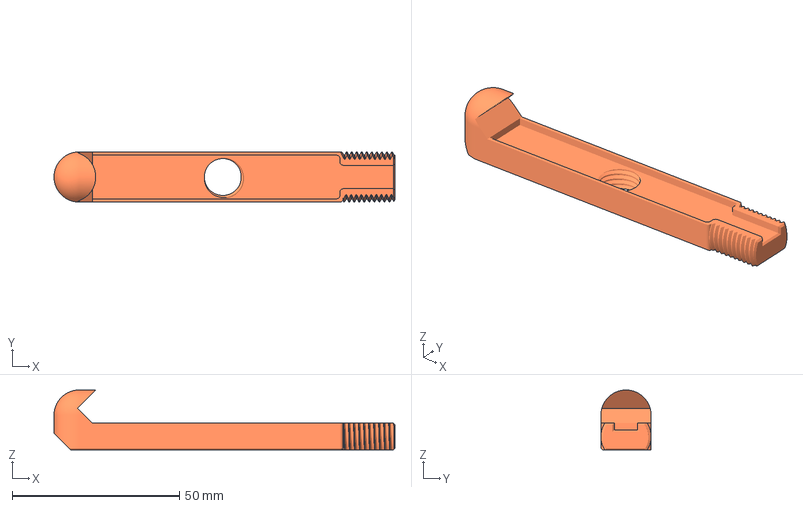
[picture p74: CAD file, 2024-01-22]
3D-Models/Mounts/Clamps/Smartphone Models/Galaxy S22 Ultra/DoomScroller - Clamp frame-Galaxy S22 Ultra.3mf
101.8 x 15.0 x 17.9 mm
