jon-le0234/DoomScroller/3D-Models/Mounts/Clamps/Smartphone Models/Galaxy S22+/DoomScroller - Clamp frame-Galaxy S22+.3mf

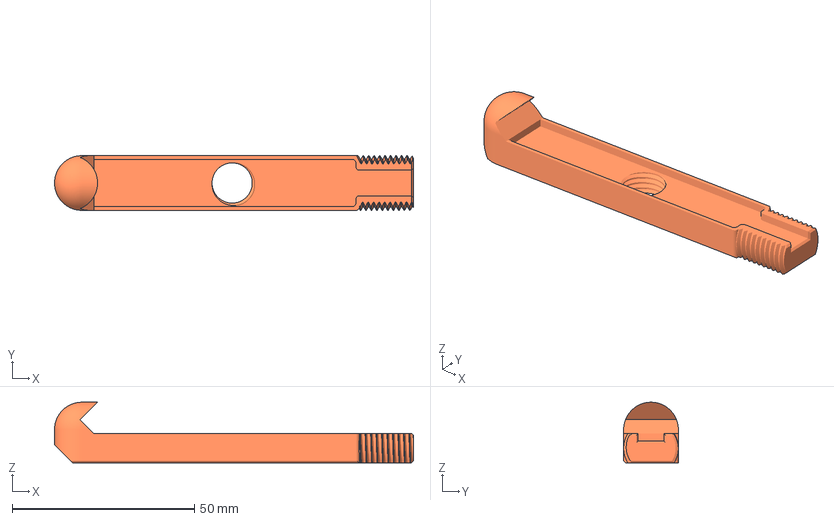
[picture p75: CAD file, 2024-01-22]
3D-Models/Mounts/Clamps/Smartphone Models/Galaxy S22+/DoomScroller - Clamp frame-Galaxy S22+.3mf
98.4 x 15.0 x 16.6 mm
