jon-le0234/DoomScroller/3D-Models/Mounts/Clamps/Smartphone Models/Galaxy S22/DoomScroller - Clamp movable jaw-Galaxy S22.3mf

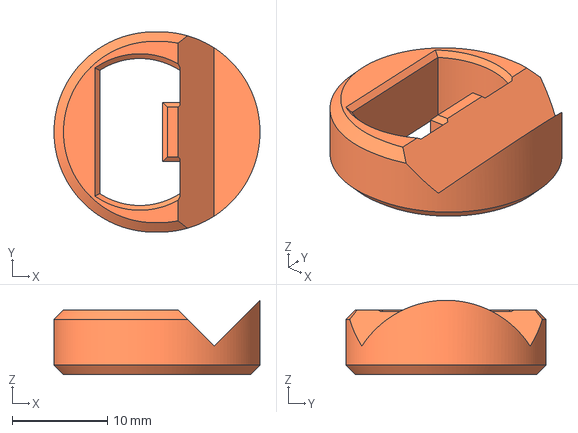
[picture p76: CAD file, 2024-01-22]
3D-Models/Mounts/Clamps/Smartphone Models/Galaxy S22/DoomScroller - Clamp movable jaw-Galaxy S22.3mf
21.6 x 21.0 x 7.80 mm
