jon-le0234/DoomScroller/3D-Models/Mounts/Clamps/Smartphone Models/Galaxy S23+/DoomScroller - Clamp frame-Galaxy S23+.3mf

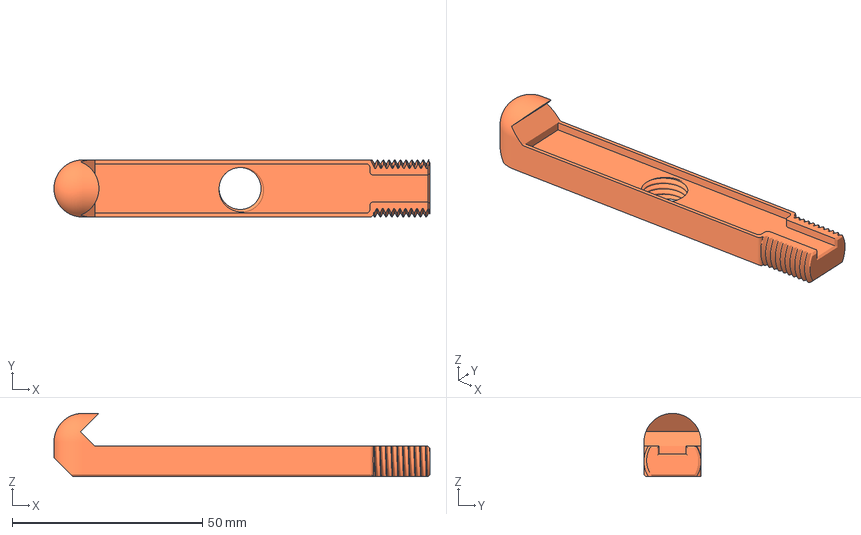
[picture p77: CAD file, 2024-01-22]
3D-Models/Mounts/Clamps/Smartphone Models/Galaxy S23+/DoomScroller - Clamp frame-Galaxy S23+.3mf
98.8 x 15.0 x 16.6 mm
