jon-le0234/DoomScroller/3D-Models/Mounts/Clamps/Smartphone Models/iPhone 12 mini/DoomScroller - Clamp movable jaw-iPhone 12 mini.3mf

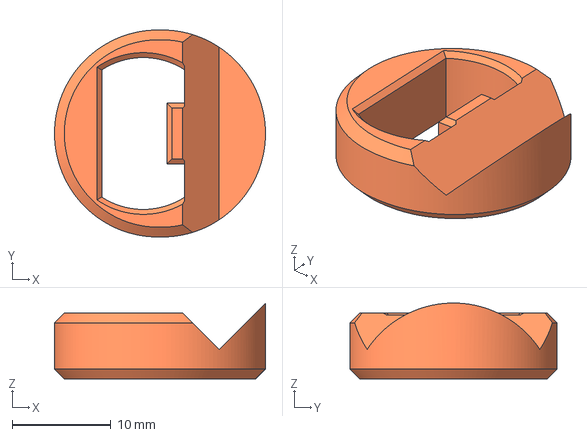
[picture p78: CAD file, 2024-01-22]
3D-Models/Mounts/Clamps/Smartphone Models/iPhone 12 mini/DoomScroller - Clamp movable jaw-iPhone 12 mini.3mf
21.4 x 21.0 x 7.70 mm
