jon-le0234/DoomScroller/3D-Models/Mounts/Clamps/Smartphone Models/iPhone 12 Pro/DoomScroller - Clamp frame-iPhone 12 Pro.3mf

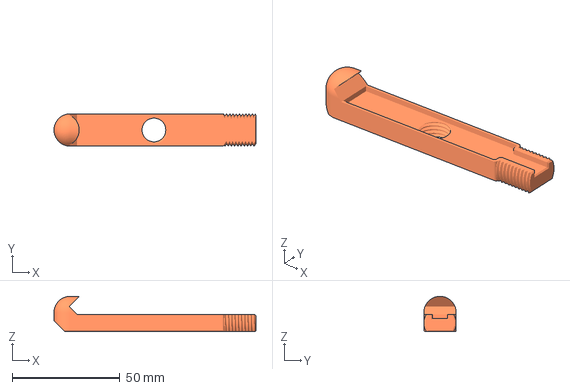
[picture p79: CAD file, 2024-01-22]
3D-Models/Mounts/Clamps/Smartphone Models/iPhone 12 Pro/DoomScroller - Clamp frame-iPhone 12 Pro.3mf
93.9 x 15.0 x 16.4 mm
