jon-le0234/DoomScroller/3D-Models/Mounts/Clamps/Smartphone Models/iPhone 13 Pro/DoomScroller - Clamp frame-iPhone 13 Pro.3mf

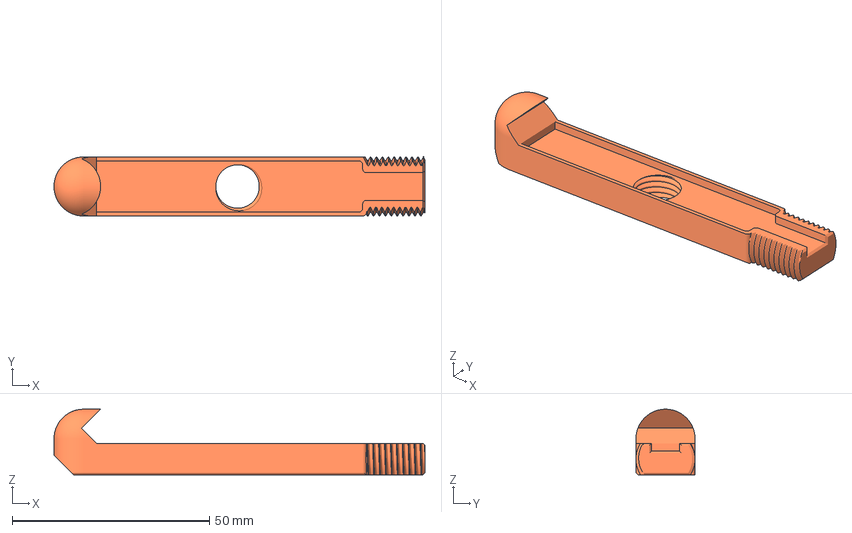
[picture p80: CAD file, 2024-01-22]
3D-Models/Mounts/Clamps/Smartphone Models/iPhone 13 Pro/DoomScroller - Clamp frame-iPhone 13 Pro.3mf
94.1 x 15.0 x 16.6 mm
