jon-le0234/DoomScroller/3D-Models/Mounts/Clamps/Smartphone Models/iPhone 5/DoomScroller - Clamp frame-iPhone 5.3mf

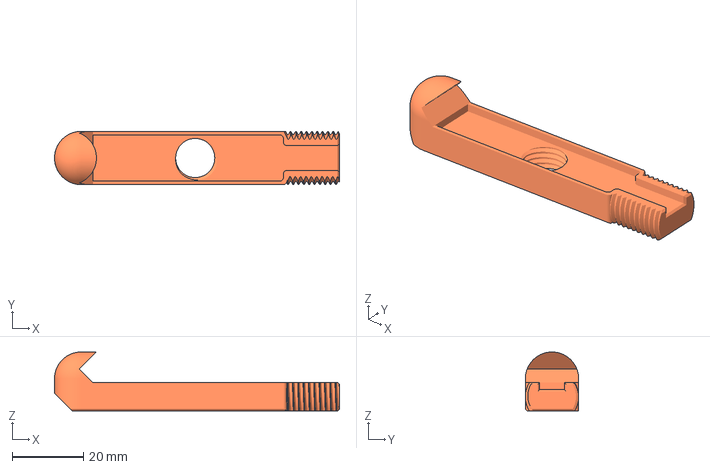
[picture p81: CAD file, 2024-01-22]
3D-Models/Mounts/Clamps/Smartphone Models/iPhone 5/DoomScroller - Clamp frame-iPhone 5.3mf
80.2 x 15.0 x 16.6 mm
