jon-le0234/DoomScroller/3D-Models/Mounts/Clamps/Smartphone Models/iPhone 5c/DoomScroller - Clamp frame-iPhone 5c.3mf

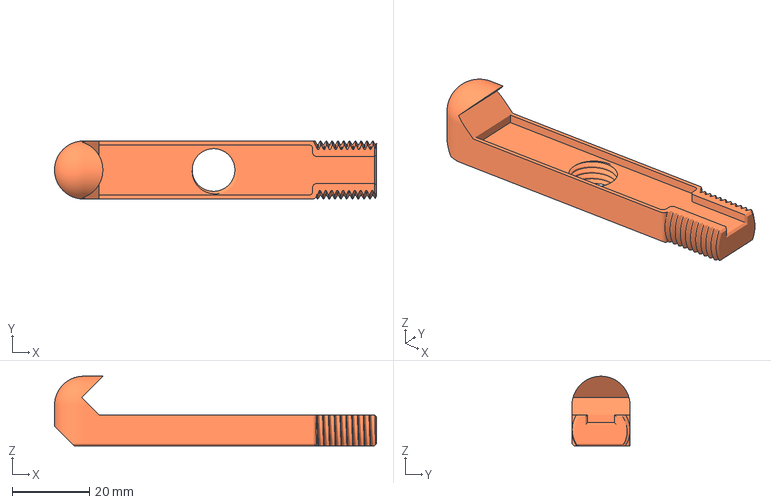
[picture p82: CAD file, 2024-01-22]
3D-Models/Mounts/Clamps/Smartphone Models/iPhone 5c/DoomScroller - Clamp frame-iPhone 5c.3mf
83.2 x 15.0 x 18.0 mm
