jon-le0234/DoomScroller/3D-Models/Mounts/Clamps/Smartphone Models/iPhone 6 Plus/DoomScroller - Clamp frame-iPhone 6 Plus.3mf

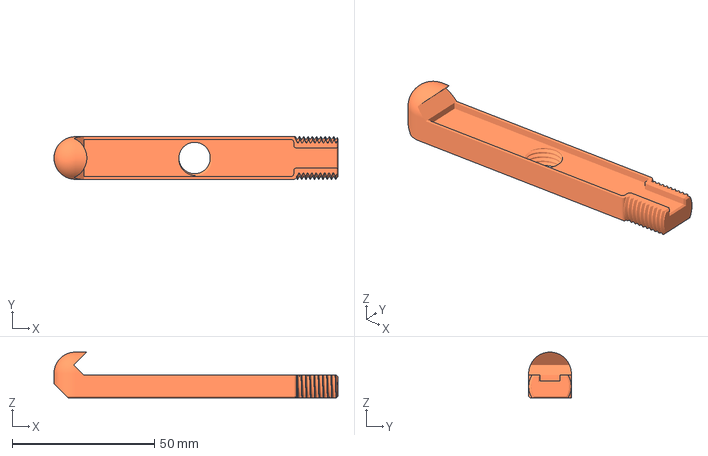
[picture p83: CAD file, 2024-01-22]
3D-Models/Mounts/Clamps/Smartphone Models/iPhone 6 Plus/DoomScroller - Clamp frame-iPhone 6 Plus.3mf
99.9 x 15.0 x 16.1 mm
