jon-le0234/DoomScroller/3D-Models/Mounts/Clamps/Smartphone Models/iPhone 6/DoomScroller - Clamp movable jaw-iPhone 6.3mf

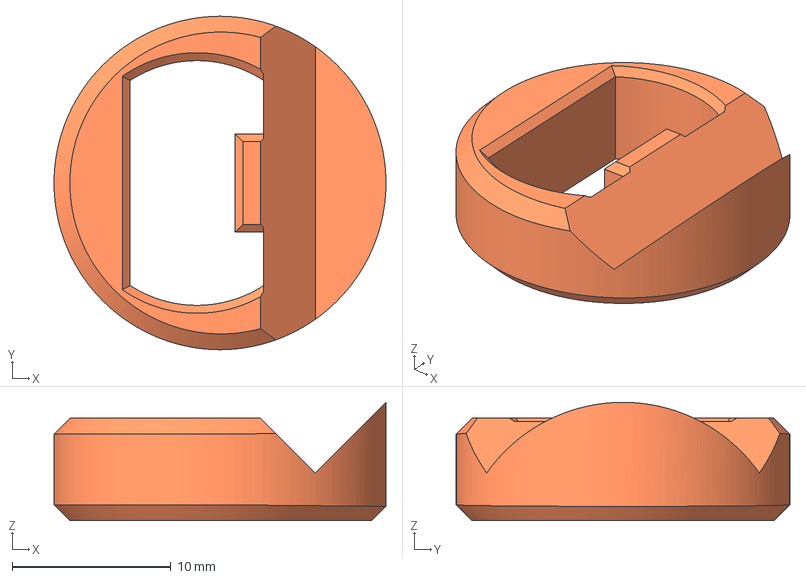
[picture p84: CAD file, 2024-01-22]
3D-Models/Mounts/Clamps/Smartphone Models/iPhone 6/DoomScroller - Clamp movable jaw-iPhone 6.3mf
20.9 x 21.0 x 7.45 mm
