jon-le0234/DoomScroller/3D-Models/Mounts/Clamps/Smartphone Models/iPhone 6s Plus/DoomScroller - Clamp movable jaw-iPhone 6s Plus.3mf

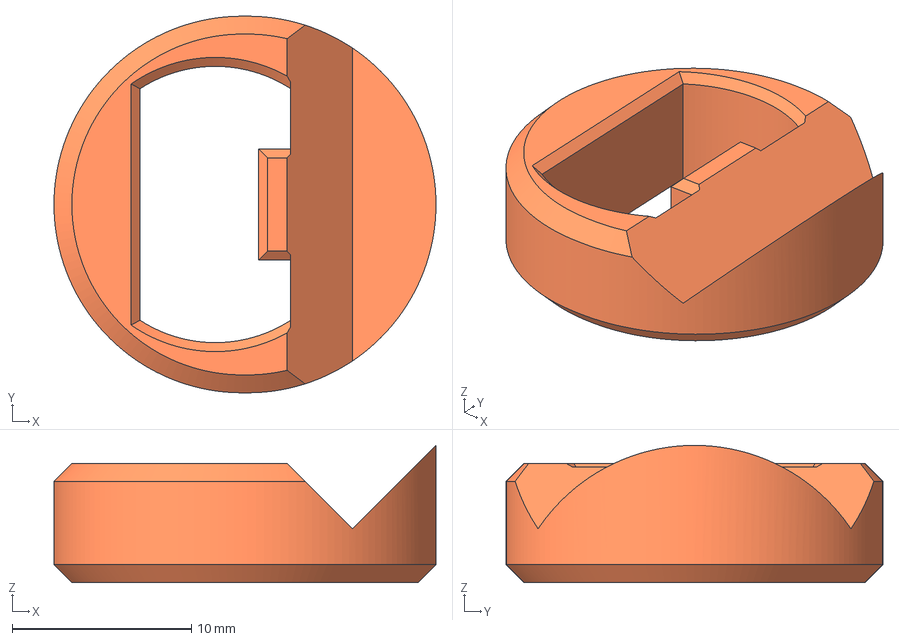
[picture p85: CAD file, 2024-01-22]
3D-Models/Mounts/Clamps/Smartphone Models/iPhone 6s Plus/DoomScroller - Clamp movable jaw-iPhone 6s Plus.3mf
21.3 x 21.0 x 7.65 mm
