jon-le0234/DoomScroller/3D-Models/Mounts/Clamps/Smartphone Models/iPhone 6s/DoomScroller - Clamp frame-iPhone 6s.3mf

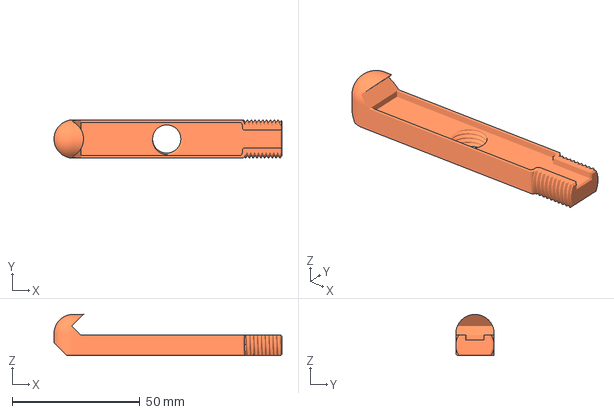
[picture p86: CAD file, 2024-01-22]
3D-Models/Mounts/Clamps/Smartphone Models/iPhone 6s/DoomScroller - Clamp frame-iPhone 6s.3mf
89.2 x 15.0 x 16.1 mm
