jon-le0234/DoomScroller/3D-Models/Mounts/Clamps/Smartphone Models/iPhone 8 Plus/DoomScroller - Clamp movable jaw-iPhone 8 Plus.3mf

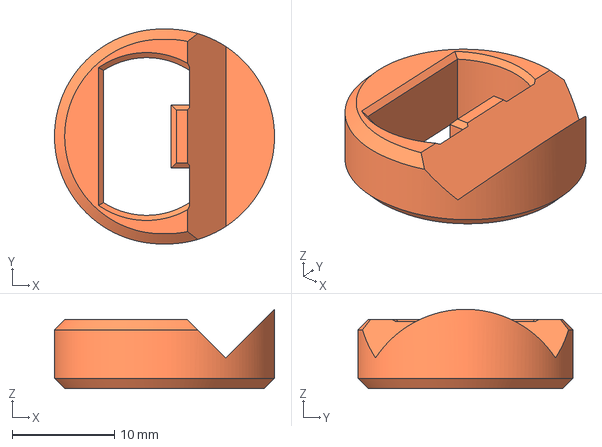
[picture p87: CAD file, 2024-01-22]
3D-Models/Mounts/Clamps/Smartphone Models/iPhone 8 Plus/DoomScroller - Clamp movable jaw-iPhone 8 Plus.3mf
21.5 x 21.0 x 7.75 mm
