jon-le0234/DoomScroller/3D-Models/Mounts/Clamps/Smartphone Models/iPhone 8/DoomScroller - Clamp frame-iPhone 8.3mf

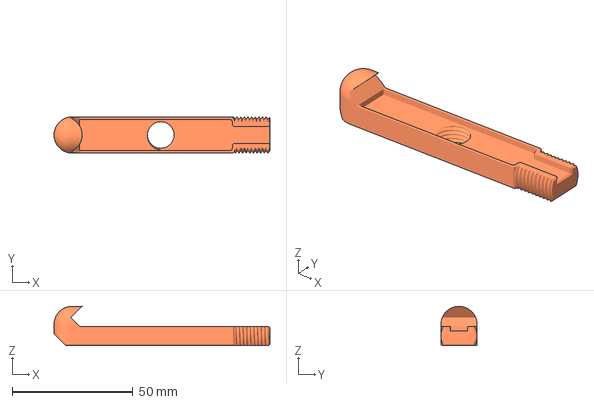
[picture p88: CAD file, 2024-01-22]
3D-Models/Mounts/Clamps/Smartphone Models/iPhone 8/DoomScroller - Clamp frame-iPhone 8.3mf
89.6 x 15.0 x 16.3 mm
