jon-le0234/DoomScroller/3D-Models/Mounts/Clamps/Smartphone Models/iPhone SE 1/DoomScroller - Clamp frame-iPhone SE 1.3mf

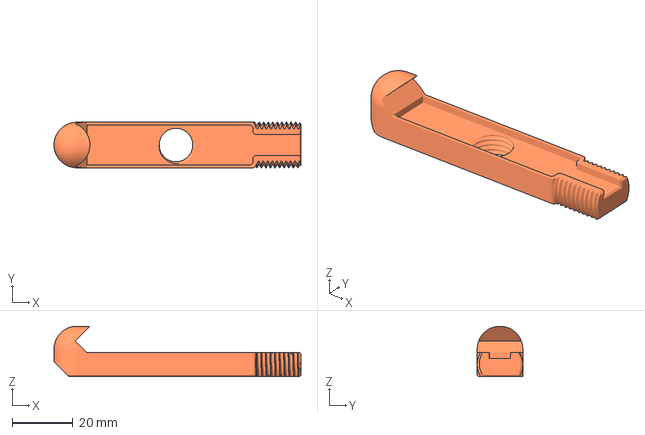
[picture p89: CAD file, 2024-01-22]
3D-Models/Mounts/Clamps/Smartphone Models/iPhone SE 1/DoomScroller - Clamp frame-iPhone SE 1.3mf
81.2 x 15.0 x 16.6 mm
