jon-le0234/DoomScroller/3D-Models/Mounts/Clamps/Smartphone Models/iPhone XR/DoomScroller - Clamp movable jaw-iPhone XR.3mf

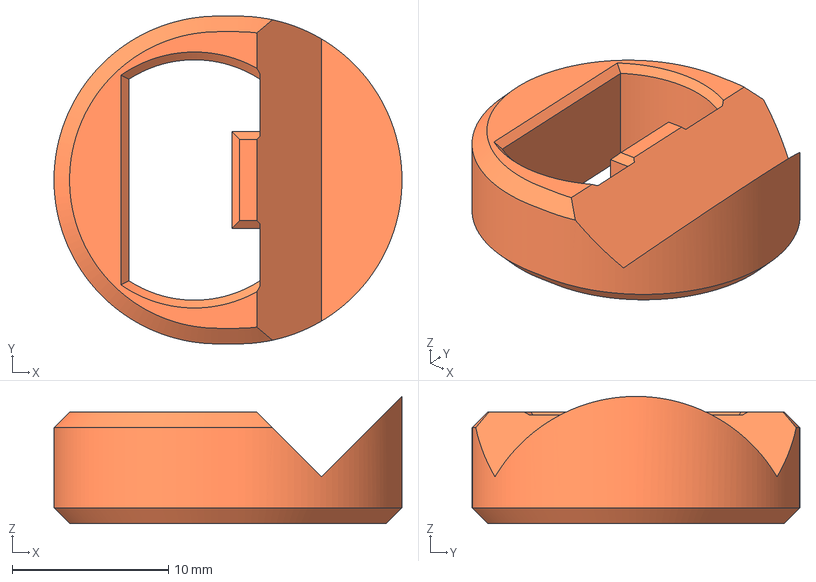
[picture p90: CAD file, 2024-01-22]
3D-Models/Mounts/Clamps/Smartphone Models/iPhone XR/DoomScroller - Clamp movable jaw-iPhone XR.3mf
22.3 x 21.0 x 8.15 mm
