jon-le0234/DoomScroller/3D-Models/Mounts/Clamps/Smartphone Models/iPhone XS Max/DoomScroller - Clamp frame-iPhone XS Max.3mf

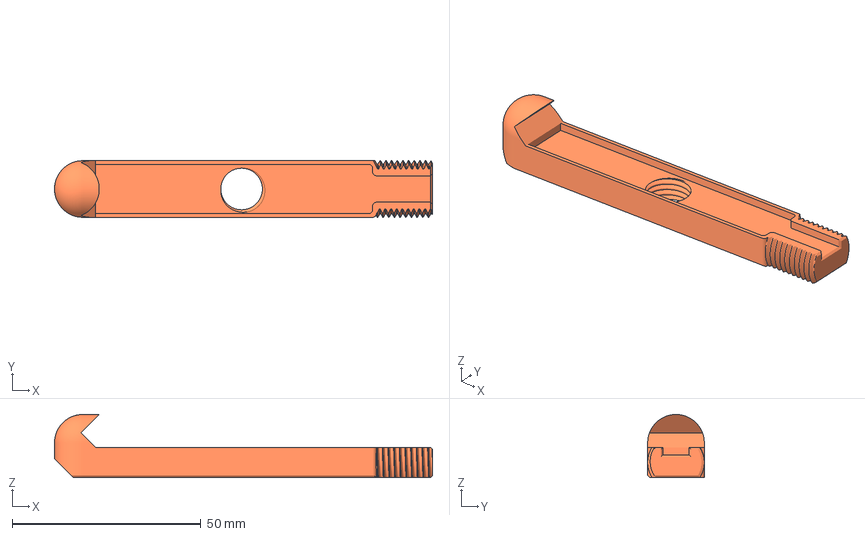
[picture p91: CAD file, 2024-01-22]
3D-Models/Mounts/Clamps/Smartphone Models/iPhone XS Max/DoomScroller - Clamp frame-iPhone XS Max.3mf
100.1 x 15.0 x 16.7 mm
