jon-le0234/DoomScroller/3D-Models/Mounts/Clamps/Tablets/7h DoomScroller - Frame base for iPad Pro 11.3mf

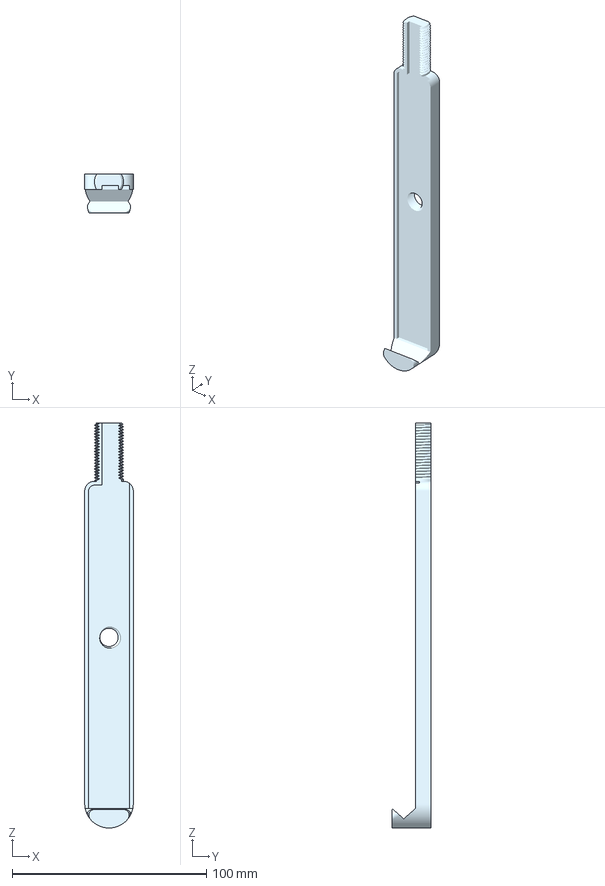
[picture p92: CAD file, 2024-01-02]
3D-Models/Mounts/Clamps/Tablets/7h DoomScroller - Frame base for iPad Pro 11.3mf
25.0 x 20.0 x 208.5 mm
