jon-le0234/DoomScroller/3D-Models/Mounts/MagFace.3mf

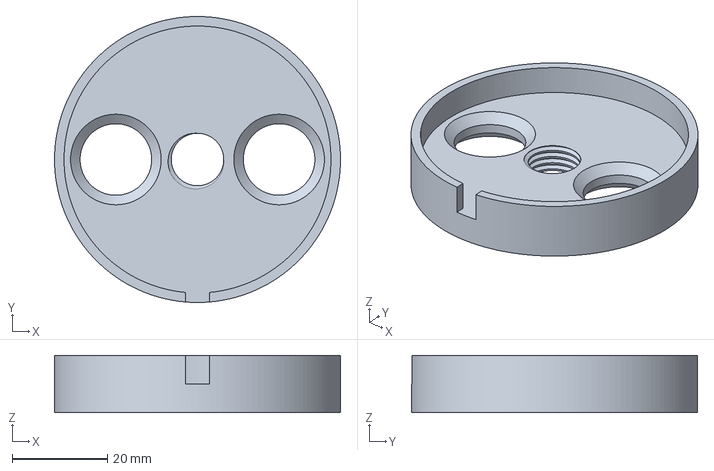
[picture p93: CAD file, 2024-01-02]
3D-Models/Mounts/MagFace.3mf
60.0 x 60.0 x 12.0 mm
