jon-le0234/DoomScroller/3D-Models/Common-Components/Mounts/Clamps/Smartphones/Mini DoomScroller - Clamp frame iPhone 15 Pro Max.3mf

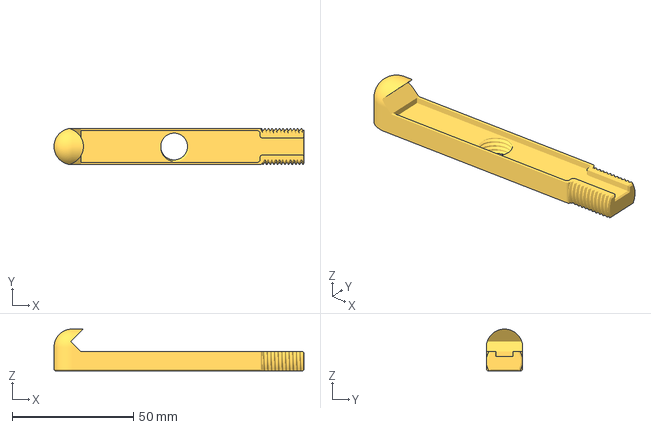
[picture p94: CAD file, 2024-01-10]
3D-Models/Common-Components/Mounts/Clamps/Smartphones/Mini DoomScroller - Clamp frame iPhone 15 Pro Max.3mf
103.0 x 15.0 x 17.2 mm
