jon-le0234/DoomScroller/3D-Models/DoomScroller/Hips/2b DoomScroller Hip - PanaVise 300 305.3mf

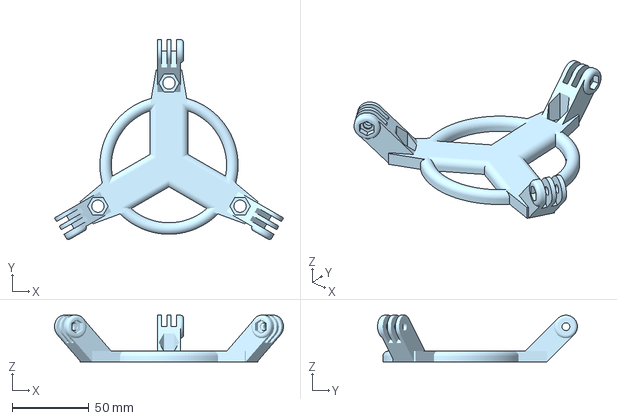
[picture p95: CAD file, 2024-01-02]
3D-Models/DoomScroller/Hips/2b DoomScroller Hip - PanaVise 300 305.3mf
149.2 x 130.2 x 30.4 mm
