jon-le0234/DoomScroller/3D-Models/DoomScroller/Legs/1c DoomScroller - Leg 75.3mf

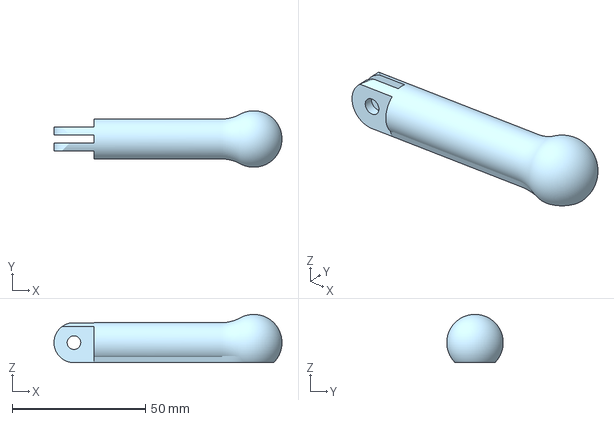
[picture p96: CAD file, 2024-01-02]
3D-Models/DoomScroller/Legs/1c DoomScroller - Leg 75.3mf
85.6 x 21.2 x 18.1 mm
