jon-le0234/DoomScroller/3D-Models/DoomScroller/Necks/3b DoomScroller - Neck PanaVise 300 305.3mf

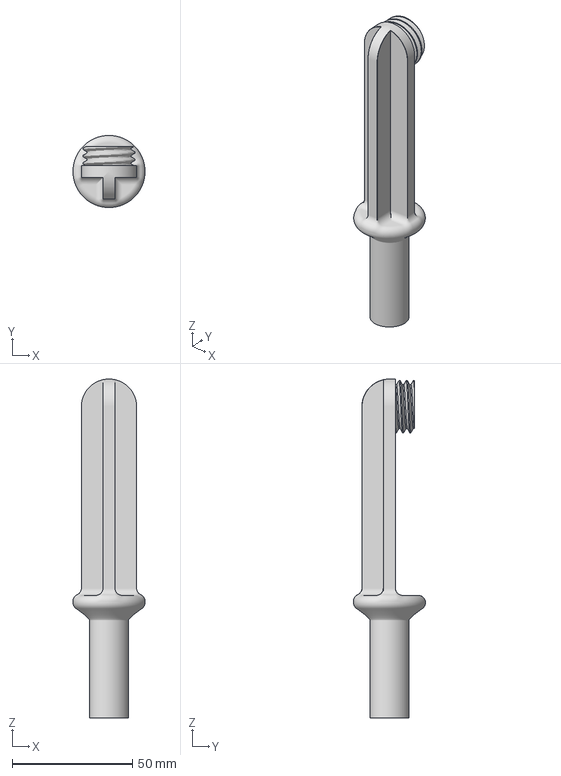
[picture p97: CAD file, 2024-01-02]
3D-Models/DoomScroller/Necks/3b DoomScroller - Neck PanaVise 300 305.3mf
30.0 x 30.0 x 141.0 mm
