jon-le0234/DoomScroller/3D-Models/Mini DoomScroller/Mini DoomScroller - Left leg.3mf

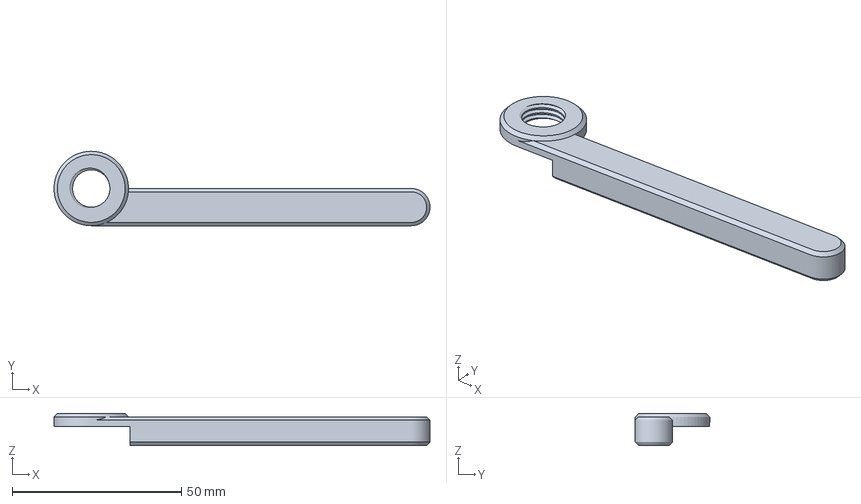
[picture p98: CAD file, 2024-12-05]
3D-Models/Mini DoomScroller/Mini DoomScroller - Left leg.3mf
111.0 x 22.0 x 9.50 mm
