jon-le0234/DoomScroller/3D-Models/Mounts/7b DoomScroller - MagFace iPhone Pro Max.stl

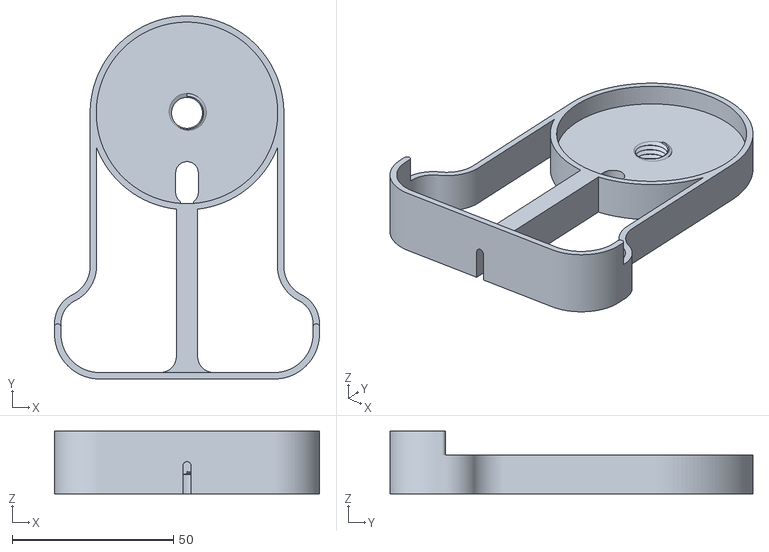
[picture p99: CAD file, 2024-01-02]
3D-Models/Mounts/7b DoomScroller - MagFace iPhone Pro Max.stl
82.1 x 112.4 x 19.5
