jon-le0234/DoomScroller/3D-Models/Mounts/Clamps/Game Console/Nintendo Switch OLED/DoomScroller - Clamp frame-Nintendo Switch OLED.3mf

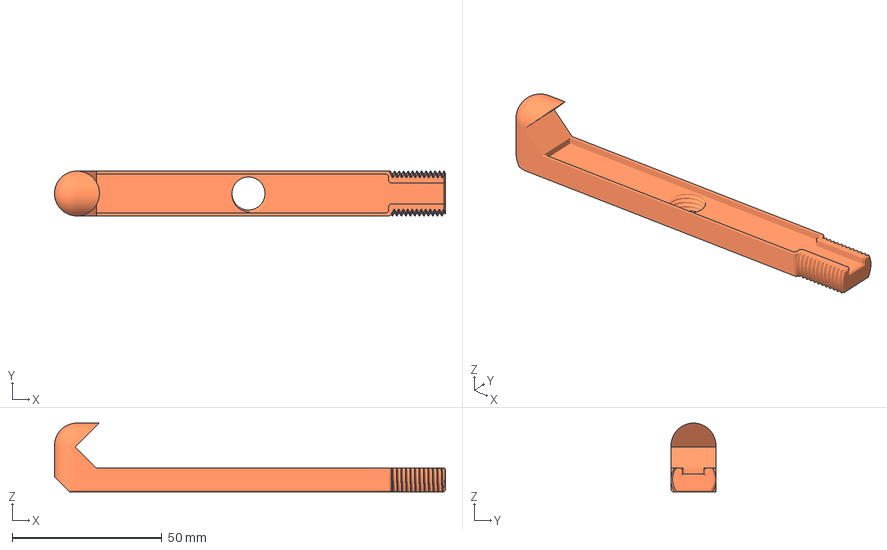
[picture p100: CAD file, 2024-01-22]
3D-Models/Mounts/Clamps/Game Console/Nintendo Switch OLED/DoomScroller - Clamp frame-Nintendo Switch OLED.3mf
130.6 x 15.0 x 23.0 mm
