jon-le0234/DoomScroller/3D-Models/Mounts/Clamps/General Smartphone/Caseless/DoomScroller - Clamp frame-Smartphone 9-85-5.3mf

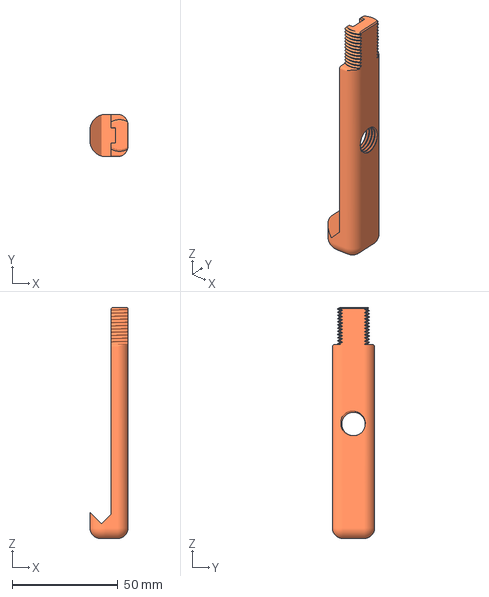
[picture p101: CAD file, 2024-12-05]
3D-Models/Mounts/Clamps/General Smartphone/Caseless/DoomScroller - Clamp frame-Smartphone 9-85-5.3mf
18.0 x 20.0 x 109.0 mm
