jon-le0234/DoomScroller/3D-Models/Mounts/Clamps/Smartphone Models/Galaxy S20 Ultra 5G/DoomScroller - Clamp movable jaw-Galaxy S20 Ultra 5G.3mf

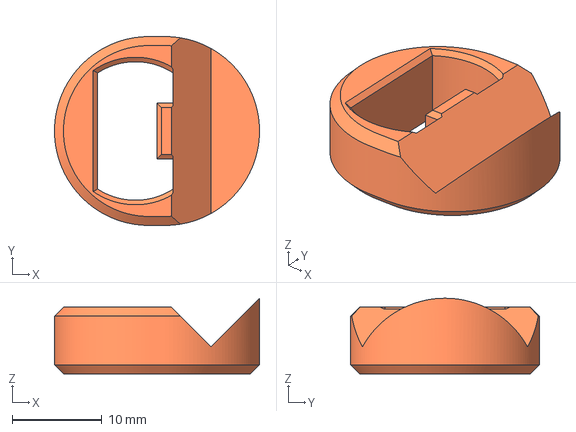
[picture p105: CAD file, 2024-01-22]
3D-Models/Mounts/Clamps/Smartphone Models/Galaxy S20 Ultra 5G/DoomScroller - Clamp movable jaw-Galaxy S20 Ultra 5G.3mf
22.8 x 21.0 x 8.40 mm
