jon-le0234/DoomScroller/3D-Models/Mounts/Clamps/Smartphone Models/iPhone 12 mini/DoomScroller - Clamp frame-iPhone 12 mini.3mf

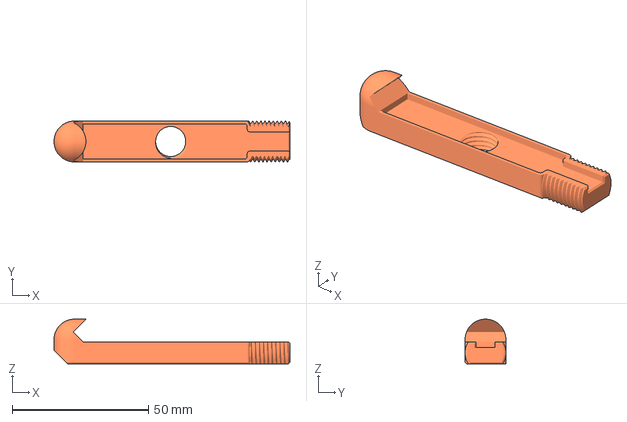
[picture p107: CAD file, 2024-01-22]
3D-Models/Mounts/Clamps/Smartphone Models/iPhone 12 mini/DoomScroller - Clamp frame-iPhone 12 mini.3mf
86.6 x 15.0 x 16.4 mm
