jon-le0234/DoomScroller/3D-Models/Mounts/Clamps/Smartphone Models/iPhone 13 mini/DoomScroller - Clamp frame-iPhone 13 mini.3mf

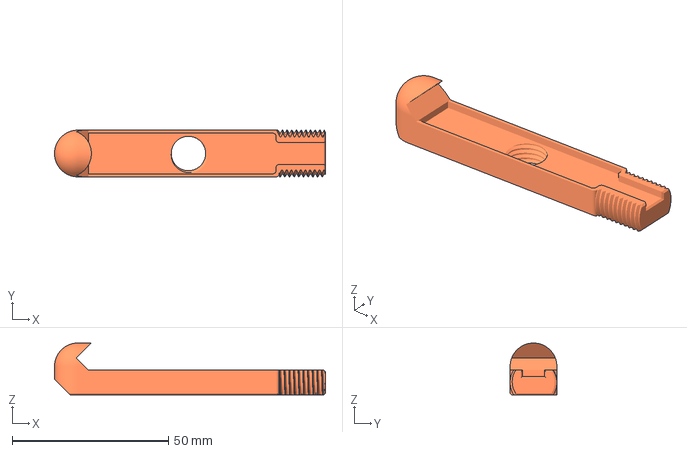
[picture p108: CAD file, 2024-01-22]
3D-Models/Mounts/Clamps/Smartphone Models/iPhone 13 mini/DoomScroller - Clamp frame-iPhone 13 mini.3mf
86.9 x 15.0 x 16.6 mm
