jon-le0234/DoomScroller/3D-Models/Mounts/Clamps/Smartphone Models/iPhone 5c/DoomScroller - Clamp movable jaw-iPhone 5c.3mf

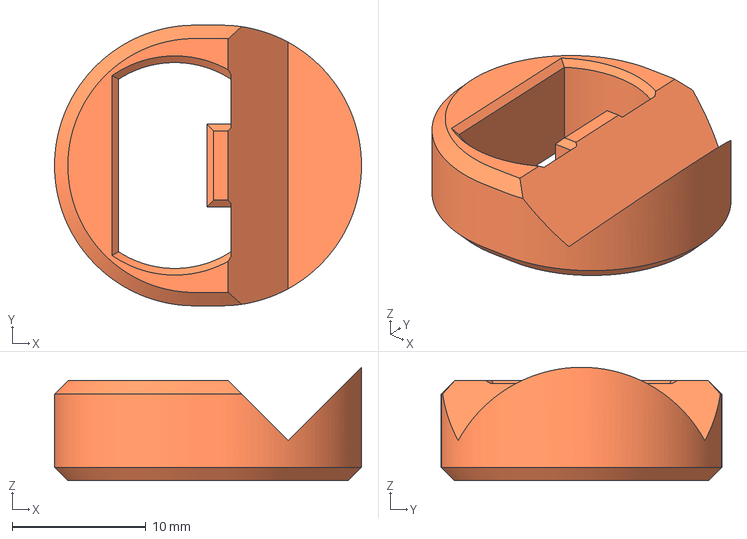
[picture p109: CAD file, 2024-01-22]
3D-Models/Mounts/Clamps/Smartphone Models/iPhone 5c/DoomScroller - Clamp movable jaw-iPhone 5c.3mf
23.0 x 21.0 x 8.48 mm
