jon-le0234/DoomScroller/3D-Models/Mounts/Clamps/Smartphone Models/iPhone 6/DoomScroller - Clamp frame-iPhone 6.3mf

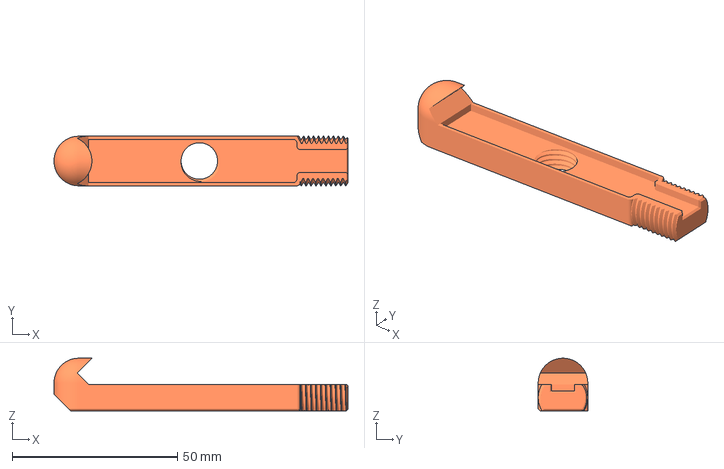
[picture p110: CAD file, 2024-01-22]
3D-Models/Mounts/Clamps/Smartphone Models/iPhone 6/DoomScroller - Clamp frame-iPhone 6.3mf
88.9 x 15.0 x 15.9 mm
