jon-le0234/DoomScroller/3D-Models/Mounts/Clamps/Smartphone Models/iPhone 8 Plus/DoomScroller - Clamp frame-iPhone 8 Plus.3mf

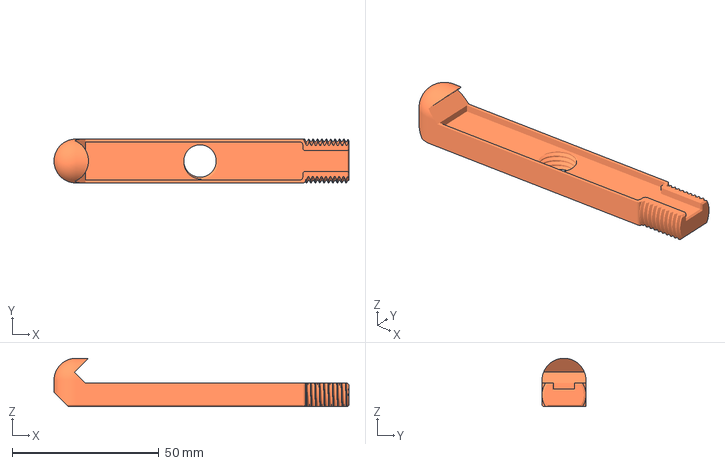
[picture p111: CAD file, 2024-01-22]
3D-Models/Mounts/Clamps/Smartphone Models/iPhone 8 Plus/DoomScroller - Clamp frame-iPhone 8 Plus.3mf
100.6 x 15.0 x 16.5 mm
