jon-le0234/DoomScroller/3D-Models/Mounts/Clamps/Tablets/7g DoomScroller - Frame base for iPad.3mf

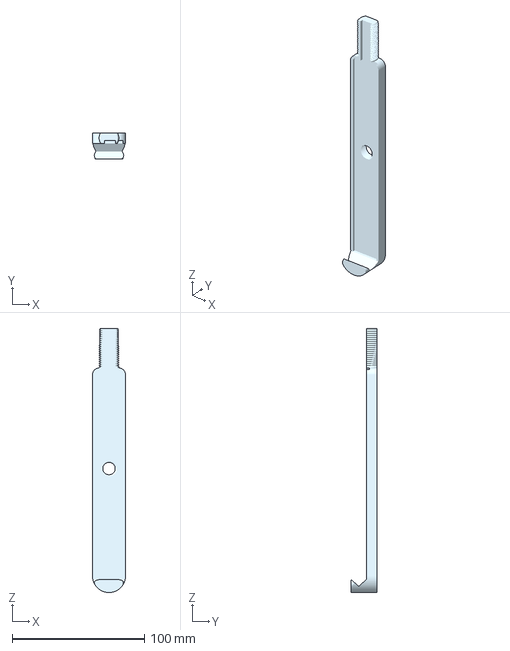
[picture p112: CAD file, 2024-01-02]
3D-Models/Mounts/Clamps/Tablets/7g DoomScroller - Frame base for iPad.3mf
25.0 x 20.0 x 200.0 mm
