jon-le0234/DoomScroller/3D-Models/Common-Components/Mounts/Clamps/Smartphones/7e DoomScroller - Frame base for iPhone mini.stl

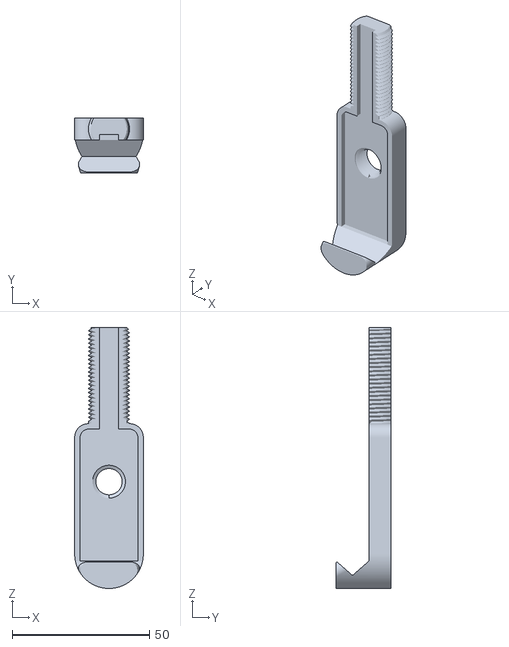
[picture p113: CAD file, 2024-01-02]
3D-Models/Common-Components/Mounts/Clamps/Smartphones/7e DoomScroller - Frame base for iPhone mini.stl
25.0 x 20.0 x 95.0
