jon-le0234/DoomScroller/3D-Models/DoomScroller/Legs/1b DoomScroller - Leg 220.stl

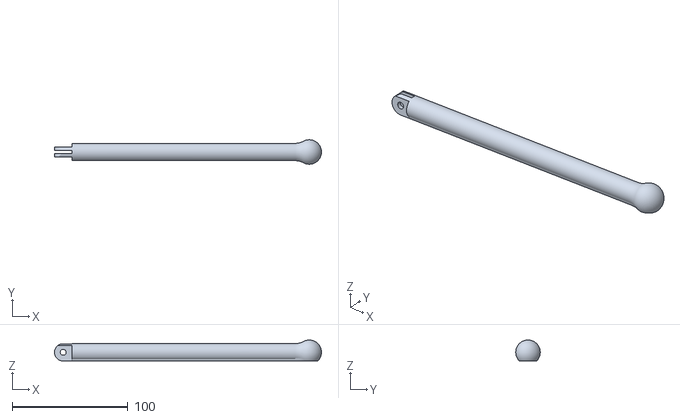
[picture p114: CAD file, 2024-01-02]
3D-Models/DoomScroller/Legs/1b DoomScroller - Leg 220.stl
230.6 x 21.2 x 18.1
