jon-le0234/DoomScroller/3D-Models/Mini DoomScroller/Mini DoomScroller - Right leg.3mf

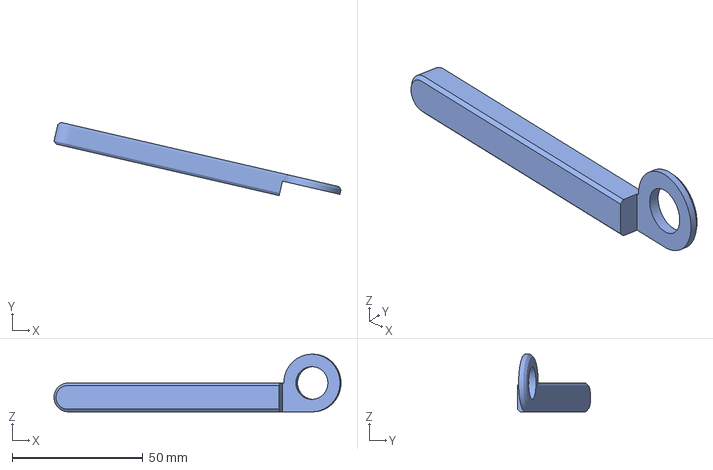
[picture p115: CAD file, 2024-12-05]
3D-Models/Mini DoomScroller/Mini DoomScroller - Right leg.3mf
109.6 x 28.0 x 22.0 mm
