jon-le0234/DoomScroller/3D-Models/Mounts/Clamps/General Smartphone/Encased/DoomScroller - Clamp frame-Smartphone case 12-75-10.3mf

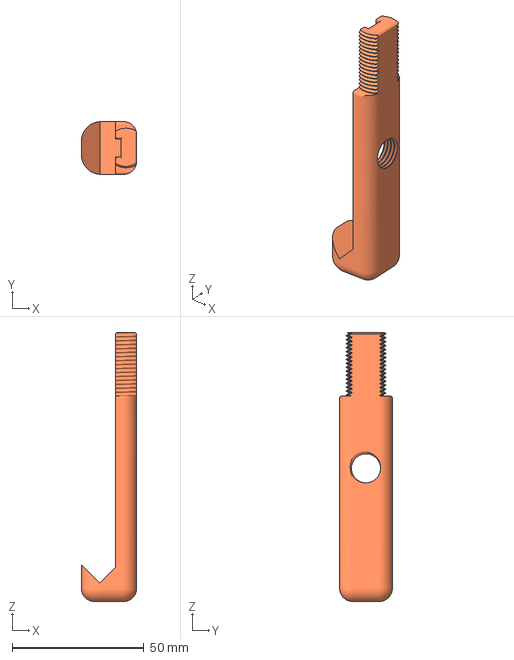
[picture p117: CAD file, 2024-12-05]
3D-Models/Mounts/Clamps/General Smartphone/Encased/DoomScroller - Clamp frame-Smartphone case 12-75-10.3mf
21.0 x 20.0 x 102.0 mm
