jon-le0234/DoomScroller/3D-Models/Mounts/Clamps/Tablets/7f DoomScroller - Frame base for iPad mini.3mf

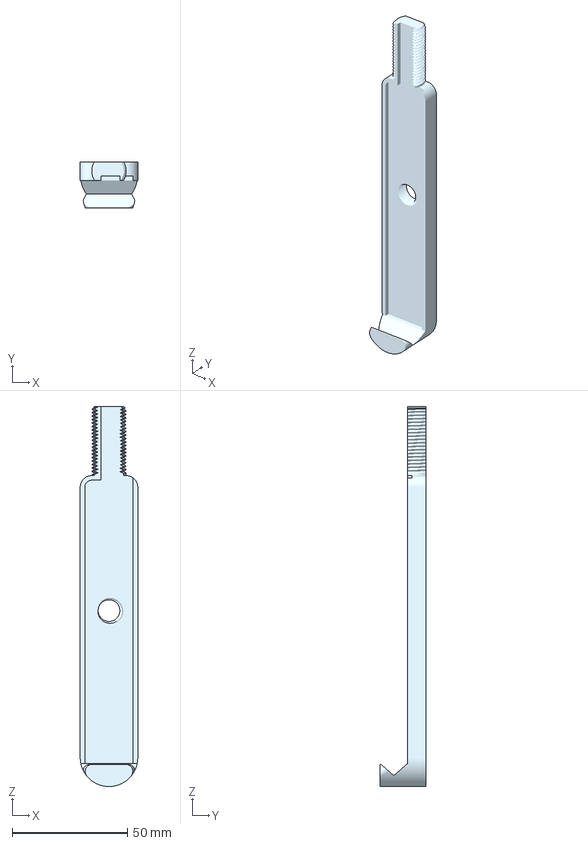
[picture p118: CAD file, 2024-01-02]
3D-Models/Mounts/Clamps/Tablets/7f DoomScroller - Frame base for iPad mini.3mf
25.0 x 20.0 x 165.0 mm
