jon-le0234/DoomScroller/3D-Models/Common-Components/Mounts/Clamps/Smartphones/7d DoomScroller - Frame base for iPhone Pro Max.stl

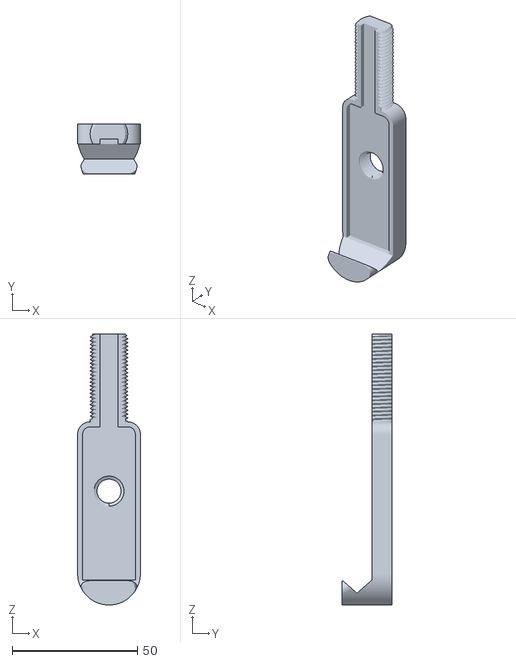
[picture p119: CAD file, 2024-01-02]
3D-Models/Common-Components/Mounts/Clamps/Smartphones/7d DoomScroller - Frame base for iPhone Pro Max.stl
25.0 x 20.0 x 108.0
