jon-le0234/DoomScroller/3D-Models/Mini DoomScroller/Mini DoomScroller - Torso.3mf

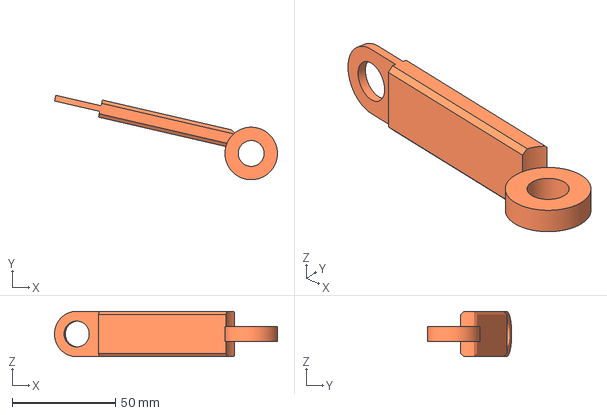
[picture p120: CAD file, 2024-12-05]
3D-Models/Mini DoomScroller/Mini DoomScroller - Torso.3mf
108.0 x 40.9 x 22.0 mm
