jon-le0234/DoomScroller/3D-Models/Mounts/Clamps/Tablets/7i DoomScroller - Frame base for iPad Pro 12.9.3mf

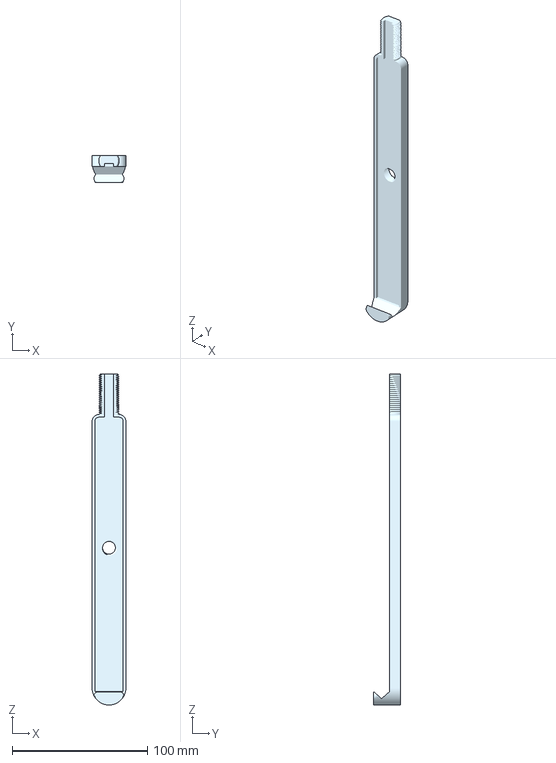
[picture p123: CAD file, 2024-01-02]
3D-Models/Mounts/Clamps/Tablets/7i DoomScroller - Frame base for iPad Pro 12.9.3mf
25.0 x 20.0 x 245.0 mm
