jon-le0234/DoomScroller/3D-Models/Mounts/Clamps/General Smartphone/Caseless/DoomScroller - Clamp movable jaw-Smartphone 9-75-5.3mf

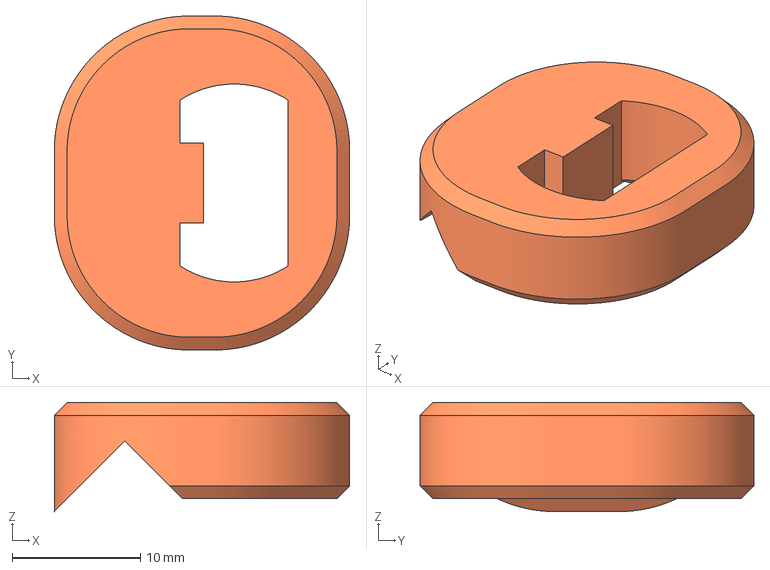
[picture p124: CAD file, 2024-12-05]
3D-Models/Mounts/Clamps/General Smartphone/Caseless/DoomScroller - Clamp movable jaw-Smartphone 9-75-5.3mf
23.0 x 26.0 x 8.50 mm
