jon-le0234/DoomScroller/3D-Models/Mounts/Clamps/General Smartphone/Encased/DoomScroller - Clamp movable jaw-Smartphone case 12-75-10.3mf

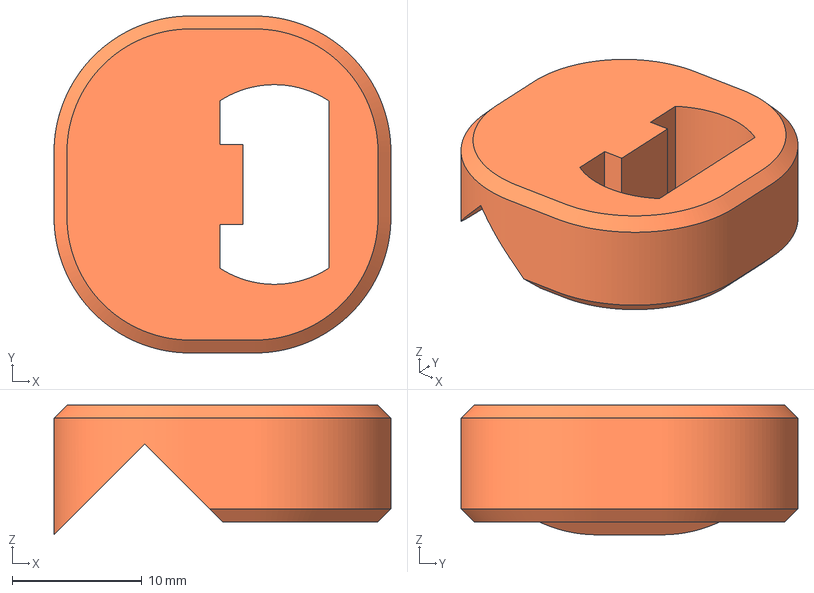
[picture p125: CAD file, 2024-12-05]
3D-Models/Mounts/Clamps/General Smartphone/Encased/DoomScroller - Clamp movable jaw-Smartphone case 12-75-10.3mf
26.0 x 26.0 x 10.0 mm
